NXP-Robotics/MR-NAVQ95/Design-files/Prototypes/Rev-B/96100_X-MR-NAVQ95E-CAM_B/BOM-96100_B.xlsx

X-MR-NAVQ95E-CAM Revised: Friday, January 16, 2026
SCH-96100 PDF: SPF-96100 Revision: B
Bill Of Materials January 16,2026 14:46:54 | Page1
Item | Quantity | AgilePN | ASSY_OPT | FIND# | PRE_APN | Reference | MFG_NAME01 | MFG_PN01 | Description
______________________________________________
1 | 4 | 280-10222 |  |  |  | BH1,BH2,BH3,BH4 |  |  | MOUNTING HOLE DRILL 3.7MM PAD 6MM PLATED TH NO PART TO ORDER
2 | 6 | 150-79025 |  |  |  | C6,C10,C11,C12,C13,C14 | MURATA | GCM155R71C104KA55D | CAP CER 0.1uF 16V 10% X7R AEC-Q200 0402
3 | 3 | 150-81359 |  |  |  | C7,C8,C9 | MURATA | GRM155Z71A105KE01J | CAP CER 1uF 10V 10% X7R 0402
4 | 4 | 480-79837 |  |  |  | D1,D2,D3,D4 | NEXPERIA | IP4292CZ10-TBR,115 | DIODE ESD TVS ARRAY USB2 USB3 5.5V 4A DFN2510A-10
5 | 1 | 480-78454 |  |  |  | D5 | NEXPERIA | PESD5V0F1BL,315 | DIODE BIDIR 1-LINE ESD PROT 0.4pF 6V 2.5A AEC-Q101 SOD882
6 | 2 | 150-81001 |  |  |  | FL1,FL2 | MURATA | NFM15PC104R1A3D | CAP FILTER EMI 0.1uF 10V 20% -- 0402
7 | 1 | 211-10508 |  |  |  | J1 | HIROSE | DF40TC-40DP-0.4V(51) | CON 2X20 PLUG SHRD SMT 0.4MM SP 51H AU
8 | 1 | 211-10530 |  |  |  | J3 | AMPHENOL | F32Q-1A7H1-11022 | CON 1X22 FPC/FFC RA SMT UPPER CONTACT 0.5MM SP 87H AU
9 | 1 | 210-80138 | DNP |  |  | J4 | SAMTEC | TSW-103-08-F-S-RA | HDR 1X3 RA TH 100MIL SP 124H AU 90L
10 | 1 | 470-82834 |  |  |  | R5 | VISHAY INTERTECHNOLOGY | CRCW0402200KFKEDC | RES MF 200K 1/16W 1% 0402
11 | 5 | 470-10144 |  |  |  | R8,R9,R10,R42,R43 | YAGEO AMERICA | AC0402JR-070RL | RES MF ZERO OHM JUMPER 1/16W 5% AEC-Q200 0402
12 | 4 | 470-82016 |  |  |  | R38,R39,R40,R41 | VISHAY INTERTECHNOLOGY | CRCW04022K20FKED | RES MF 2.2K 1/16W 1% AEC-Q200 0402
13 | 1 | 510-75618 |  |  |  | TP1 |  |  | TEST POINT PAD .035 SMT, no part to order
14 | 1 | 315-84354 |  |  |  | U1 | NXP SEMICONDUCTOR | PCA9306JKZ | IC DUAL BI I2C BUS SMBUS VOLTAGE TRANSLATOR 1-3.6V/1.8-5.5V X2SON8
