NXP-Robotics/MR-NAVQ95/Design-files/Prototypes/Rev-B/96101_X-MR-NAVQ95E-T1S_B/BOM-96101_B.xlsx

X-MR-NAVQ95E-T1S Revised: Friday, January 16, 2026
SCH-96101 PDF: SPF-96101 Revision: B
Bill Of Materials January 16,2026 14:53:41 | Page1
Item | Quantity | AgilePN | ASSY_OPT | FIND# | PRE_APN | Reference | MFG_NAME01 | MFG_PN01 | Description
______________________________________________
1 | 3 | 280-10222 |  |  |  | BH1,BH2,BH3 |  |  | MOUNTING HOLE DRILL 3.7MM PAD 6MM PLATED TH NO PART TO ORDER
2 | 1 | 150-79025 |  |  |  | C6 | MURATA | GCM155R71C104KA55D | CAP CER 0.1uF 16V 10% X7R AEC-Q200 0402
3 | 11 | 150-79497 |  |  |  | C126,C138,C139,C155,C165, | MURATA | GCM155C71A105KE38D | CAP CER 1uF 10V 10% X7S AEC-Q200 0402
 |  |  |  |  |  | C167,C173,C430,C432,C439,
 |  |  |  |  |  | C441
4 | 37 | 150-79461 |  |  |  | C127,C134,C137,C140,C146, | MURATA | GCM155R71H104KE02D | CAP CER 0.1uF 50V 10% X7R AEC-Q200 0402
 |  |  |  |  |  | C178,C423,C424,C431,C434,
 |  |  |  |  |  | C435,C444,C445,C446,C447,
 |  |  |  |  |  | C448,C449,C450,C451,C454,
 |  |  |  |  |  | C455,C457,C458,C459,C460,
 |  |  |  |  |  | C461,C462,C463,C464,C503,
 |  |  |  |  |  | C504,C506,C507,C508,C509,
 |  |  |  |  |  | C510,C511
5 | 2 | 150-80512 |  |  |  | C141,C505 | MURATA | GCJ21AR72E472KXJ1D | CAP CER 4700pF 250V 10% X7R AEC-Q200 0805
6 | 27 | 150-80277 |  |  |  | C149,C153,C220,C376,C378, | TDK | CGA2B3X7R1E104K050BB | CAP CER 0.1uF 25V 10% X7R AEC-Q200 0402
 |  |  |  |  |  | C389,C392,C402,C404,C425,
 |  |  |  |  |  | C426,C467,C469,C471,C477,
 |  |  |  |  |  | C479,C488,C489,C490,C491,
 |  |  |  |  |  | C492,C514,C524,C526,C527,
 |  |  |  |  |  | C528,C529
7 | 11 | 150-75772 |  |  |  | C150,C154,C169,C470,C483, | YAGEO AMERICA | CC0402KRX5R6BB105 | CAP CER 1.0UF 10V 10% X5R 0402
 |  |  |  |  |  | C484,C485,C486,C487,C515,
 |  |  |  |  |  | C530
8 | 2 | 150-80967 |  |  |  | C151,C152 | MURATA | GRT188R61C106KE13D | CAP CER 10uF 16V 10% X5R AEC-Q200 0603
9 | 2 | 150-79365 | DNP |  |  | C156,C456 | MURATA | GCM155R71E103KA37D | CAP CER 0.01uF 25V 10% X7R AEC-Q200 0402
10 | 53 | 150-80124 |  |  |  | C159,C170,C171,C172,C174, | MURATA | GRM033Z71C104KE14 | CAP CER 0.1uF 16V 10% X7R 0201
 |  |  |  |  |  | C175,C176,C177,C179,C180,
 |  |  |  |  |  | C181,C182,C183,C184,C186,
 |  |  |  |  |  | C187,C188,C191,C192,C193,
 |  |  |  |  |  | C194,C195,C196,C201,C203,
 |  |  |  |  |  | C205,C206,C207,C211,C212,
 |  |  |  |  |  | C213,C217,C218,C219,C221,
 |  |  |  |  |  | C222,C223,C226,C230,C231,
 |  |  |  |  |  | C232,C233,C234,C235,C236,
 |  |  |  |  |  | C237,C238,C472,C474,C497,
 |  |  |  |  |  | C498,C499,C500
11 | 1 | 150-79272 |  |  |  | C202 | MURATA | GRM188R61E106MA73D | CAP CER 10uF 25V 20% X5R 0603
12 | 1 | 150-78979 |  |  |  | C204 | TDK | C2012X5R1A476M125AC | CAP CER 47uF 10V 20% X5R 0805
13 | 6 | 150-80055 |  |  |  | C375,C388,C401,C422,C466, | YAGEO AMERICA | AC0603KRX7R0BB472 | CAP CER 4700pF 100V 10% X7R AEC-Q200 0603
 |  |  |  |  |  | C475
14 | 6 | 150-81481 |  |  |  | C398,C399,C403,C407,C408, | MURATA | GRT21BD71A226ME13 | CAP CER 22uF 10V 20% X7T AEC-Q200 0805
 |  |  |  |  |  | C411
15 | 2 | 150-76336 |  |  |  | C452,C468 | MURATA | GJM1555C1H8R0CB01D | CAP CER 8.0pF 50V 3.12% C0G 0402
16 | 6 | 150-80340 |  |  |  | C481,C482,C501,C502,C512, | MURATA | GCM033C70J104KE02D | CAP CER 0.1uF 6.3V 10% X7S AEC-Q200 0201
 |  |  |  |  |  | C513
17 | 3 | 150-81482 |  |  |  | C493,C495,C496 | MURATA | GRT188C71C475KE13 | CAP CER 4.7uF 16V 10% X7S AEC-Q200 0603
18 | 1 | 150-79362 |  |  |  | C494 | MURATA | GCM32ER71C226KE19L | CAP CER 22uF 16V 10% X7R AEC-Q200 1210
19 | 2 | 150-81792 |  |  |  | C516,C517 | MURATA | GCM31C5C3A102JX03 | CAP CER 1000pF 1000V 5% C0G AEC-Q200 1206
20 | 2 | 150-81359 |  |  |  | C521,C525 | MURATA | GRM155Z71A105KE01J | CAP CER 1uF 10V 10% X7R 0402
21 | 2 | 370-76859 |  |  |  | D33,D35 | WURTH ELEKTRONIK EISOS GMBH & CO. KG (ELECTRONIC & ELECTROMEHANICAL COMP) | 150060AS75000 | LED AMB SGL 2V 20mA 0603
22 | 2 | 370-76670 |  |  |  | D34,D36 | WURTH ELEKTRONIK EISOS GMBH & CO. KG (ELECTRONIC & ELECTROMEHANICAL COMP) | 150060VS75000 | LED BRIGHT GRN SGL 30mA 0603
23 | 8 | 480-80185 |  |  |  | U57,U64,D66,D68,D70,D72, | NEXPERIA | PESD2ETH1G-T | DIODE 2 CH ESD PROTECTOR 30KV 24V AEC-Q101 SOT23
 |  |  |  |  |  | D74,D76
24 | 6 | 370-76565 |  |  |  | D67,D69,D71,D73,D75,D77 | OSRAM | LG L29K-G2J1-24-Z | LED GRN SGL 20MA 0603
25 | 1 | 370-76464 |  |  |  | D79 | KINGBRIGHT | APT1608MGC | LED GRN SGL 30MA SMT
26 | 6 | 211-80595 |  |  |  | J26,J27,J28,J29,J30,J31 | JST MFG. CO | SM02B-GHS-TB(LF)(SN) | CON 1X2 CRIMP RA 1.25MM SP 173H SN SMT
27 | 2 | 210-83192 |  |  |  | J32,J35 | HARTING | 9452812800 | CON 1X2 JACK 1 PORT TH 2.8MM SP 244H -- 91L
28 | 1 | 211-10510 |  |  |  | J33 | HIROSE | DF40TC-50DP-0.4V(51) | CON 2X25 PLUG SHRD SMT 0.4MM SP 51H AU
29 | 1 | 210-80888 |  |  |  | J37 | SAMTEC | SHF-105-01-L-D-RA | CON 2X5 TH SHRD PLUG RA 50MIL CTR 225H AU 75L
30 | 3 | 180-78924 |  |  |  | LBK1,LBK2,LBK3 | TDK | TFM252012ALMAR47MTAA | IND PWR 0.47uH@1MHz 5.8A 20% AEC-Q200 SMT
31 | 10 | 180-81335 |  |  |  | L13,L14,L15,L18,L19,L21, | Murata Electronics | BLM15AG121SH1D | IND FER BEAD 120 OHM@100MHZ 0.5A 0.25 OHM 25% AEC-Q200 0402
 |  |  |  |  |  | L41,L42,L44,L46
32 | 11 | 180-78156 |  |  |  | L16,L17,L23,L48,L50,L51, | TDK | MPZ1608S331A | IND FER BEAD 330OHM@100MHZ 1.7A 0603
 |  |  |  |  |  | L52,L53,L54,L56,L57
33 | 6 | 180-78762 |  |  |  | L35,L37,L39,L40,L47,L49 | TDK | ACT1210L-201-2P-TL00 | FILTER COMMON MODE 200uH@100KHZ 70mA +30/-10% AEC-Q200 SMT
34 | 2 | 180-81135 |  |  |  | L45,L55 | MURATA | DLW32MH101XT2 | IND CHK COMMON MODE 100uH@100KHz 100mA 2.6 OHM -25-50% AEC-Q200 SMT
35 | 1 | 470-82834 |  |  |  | R5 | VISHAY INTERTECHNOLOGY | CRCW0402200KFKEDC | RES MF 200K 1/16W 1% 0402
36 | 6 | 470-82056 |  |  |  | R93,R160,R565,R605,R606, | VISHAY INTERTECHNOLOGY | CRCW0402100KJNED | RES MF 100K 1/16W 5% AEC-Q200 0402
 |  |  |  |  |  | R607
37 | 4 | 470-80911 |  |  |  | R170,R173,R229,R230 | YAGEO | RC0402FR-074K7L | RES MF 4.7K OHM 1/16W 1% 0402
38 | 1 | 470-83291 |  |  |  | R171 | YAGEO AMERICA | RC0402FR-071K2L | RES MF 1.2K 1% 1/16W 0402
39 | 2 | 470-81931 |  |  |  | R184,R561 | ROHM | ESR10EZPF1003 | RES MF 100K 0.4W 1% AEC-Q200 0805
40 | 16 | 470-81930 |  |  |  | R186,R187,R454,R462,R465, | ROHM | ESR10EZPF1001 | RES MF 1.0K 0.4W 1% AEC-Q200 0805
 |  |  |  |  |  | R470,R481,R490,R501,R517,
 |  |  |  |  |  | R532,R536,R538,R540,R559,
 |  |  |  |  |  | R560
41 | 28 | 470-80881 |  |  |  | R191,R193,R194,R195,R200, | VISHAY INTERTECHNOLOGY | CRCW040210K0FKEDHP | RES MF 10K 1/5W 1% AEC-Q200 0402
 |  |  |  |  |  | R209,R213,R215,R216,R218,
 |  |  |  |  |  | R220,R222,R223,R224,R225,
 |  |  |  |  |  | R226,R227,R228,R504,R505,
 |  |  |  |  |  | R508,R509,R512,R518,R519,
 |  |  |  |  |  | R531,R550,R601
42 | 1 | 470-81665 |  |  |  | R208 | KOA SPEER | RK73H1ETTP6491F | RES MF 6.49K 1/10W 1% AEC-Q200 0402
43 | 19 | 470-82894 |  |  |  | R211,R551,R562,R563,R571, | VISHAY | RCC04020000Z0ED | RES MF ZERO OHM 1/8W -- AEC-Q200 0402
 |  |  |  |  |  | R572,R577,R578,R579,R580,
 |  |  |  |  |  | R587,R588,R589,R604,R609,
 |  |  |  |  |  | R610,R611,R612,R613
44 | 4 | 470-77301 |  |  |  | R231,R232,R233,R234 | PANASONIC | ERJ-2GEJ681X | RES MF 680 OHM 1/16W 5% 0402
45 | 6 | 470-81181 |  |  |  | R459,R466,R489,R515,R535, | VISHAY INTERTECHNOLOGY | CRCW0603100KFKEAHP | RES MF 100K 1/4W 1% AEC-Q200 0603
 |  |  |  |  |  | R539
46 | 6 | 470-30776 |  |  |  | R464,R473,R493,R520,R537, | WALSIN TECHNOLOGY CORP. | WR04X2400FTL | RES MF 240 OHM 1/16W 1% 0402
 |  |  |  |  |  | R541
47 | 6 | 470-80881 | DNP |  |  | R506,R507,R511,R547,R548, | VISHAY INTERTECHNOLOGY | CRCW040210K0FKEDHP | RES MF 10K 1/5W 1% AEC-Q200 0402
 |  |  |  |  |  | R555
48 | 8 | 470-82894 | DNP |  |  | R552,R567,R568,R569,R584, | VISHAY | RCC04020000Z0ED | RES MF ZERO OHM 1/8W -- AEC-Q200 0402
 |  |  |  |  |  | R585,R586,R597
49 | 1 | 470-83520 |  |  |  | R558 | YAGEO | AC0402JR-07100RL | RES MF 100 OHM 1/16W 5% AEC-Q200 0402
50 | 2 | 470-81628 |  |  |  | R564,R566 | KOA SPEER | RK73H1ETTP5101F | RES MF 5.1K 1/10W 1% AEC-Q200 0402
51 | 4 | 470-81990 |  |  |  | R573,R593,R594,R596 | KOA SPEER | RK73H1ETTP1501F | RES MF 1.50K 1/10W 1% AEC-Q200 0402
52 | 2 | 470-81990 | DNP |  |  | R574,R595 | KOA SPEER | RK73H1ETTP1501F | RES MF 1.50K 1/10W 1% AEC-Q200 0402
53 | 2 | 470-10187 |  |  |  | R590,R591 | YAGEO AMERICA | VT1206FRE071ML | RES MF 1M 1/4W 1% AEC-Q200 1206
54 | 2 | 470-82544 |  |  |  | R602,R603 | YAGEO AMERICA | AC0402FR-072K2L | RES MF 2.2K 1/16W 1% AEC-Q200 0402
55 | 1 | 470-82056 | DNP |  |  | R608 | VISHAY INTERTECHNOLOGY | CRCW0402100KJNED | RES MF 100K 1/16W 5% AEC-Q200 0402
56 | 1 | 510-78644 |  |  |  | S1 | NIDEC COPAL ELECTRONICS CORP | CHS-02TA | SW SPST SLD WSH 25MA 24V DIP-2 SMT
57 | 8 | 510-75618 |  |  |  | TP21,TP22,TP245,TP248, |  |  | TEST POINT PAD .035 SMT, no part to order
 |  |  |  |  |  | TP249,TP250,TP251,TP252
58 | 1 | 312-82081 |  |  |  | U53 | ISSI | IS25LP080D-JNLE-TR | IC SERIAL FLASH MEMORY SPI 128BIT 2.30V 3.60V SOIC8 DATE CODE MUST BE 1925 OR HIGHER
59 | 2 | 312-83772 |  |  |  | U54,U55 | NXP SEMICONDUCTORS | TJA1120BHN | IC ETH PHY 3.3V AEC-Q100 HVQFN36
60 | 1 | 330-77155 |  |  |  | U58 | NXP SEMICONDUCTOR | SJA1110AEL | IC ETHERNET SW WITH EMBEDDED PHYS AND CPU 3.3V AUTO BGA256A
61 | 1 | 315-10678 |  |  |  | U63 | NXP SEMICONDUCTOR | PPF5103AMMAFES | IC POWER MANAGEMENT 5.5V AEC-Q100 QFN28
62 | 1 | 315-84354 |  |  |  | U65 | NXP SEMICONDUCTOR | PCA9306JKZ | IC DUAL BI I2C BUS SMBUS VOLTAGE TRANSLATOR 1-3.6V/1.8-5.5V X2SON8
63 | 1 | 230-78230 |  |  |  | X1 | MURATA | XRCGB25M000F3A00R0 | XTAL 25.000MHZ 30PPM 6PF AEC-Q200 SMT
