NXP-Robotics/MR-NAVQ95/MR-NAVQ95-cheatsheet.pdf

MR-NAVQ95 PINOUT CHEAT SHEET | IO expansion board (NAVQ95-IO) | SHEET 1 / 2

## J9 PWM

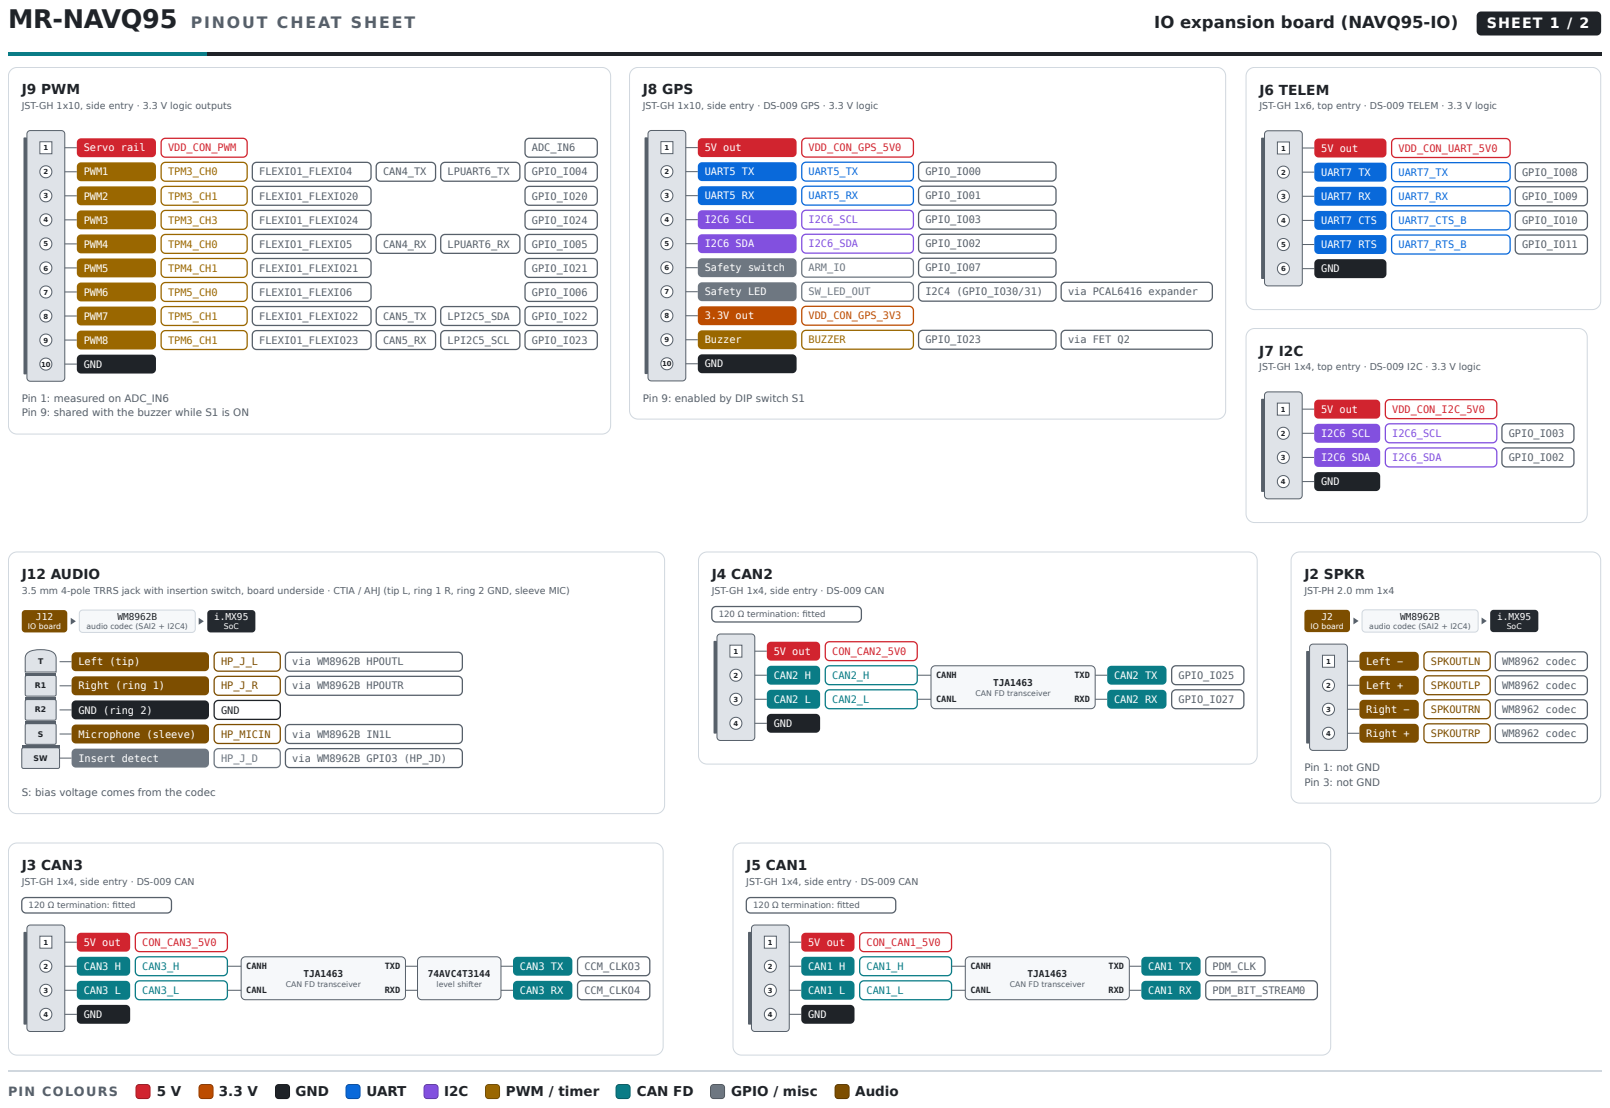
[picture p48: page 1]

J8 GPS
JST-GH 1x10, side entry · DS-009 GPS · 3.3 V logic

J6 TELEM
JST-GH 1x6, top entry · DS-009 TELEM · 3.3 V logic

JST-GH 1x10, side entry · 3.3 V logic outputs

JST-GH 1x4, top entry · DS-009 I2C · 3.3 V logic

Pin 1: measured on ADC_IN6
Pin 9: shared with the buzzer while S1 is ON

Pin 9: enabled by DIP switch S1

J12 AUDIO
3.5 mm 4-pole TRRS jack with insertion switch, board underside · CTIA / AHJ (tip L, ring 1 R, ring 2 GND, sleeve MIC)

J4 CAN2
JST-GH 1x4, side entry · DS-009 CAN

S: bias voltage comes from the codec

J3 CAN3

J5 CAN1

MR-NAVQ95 PINOUT CHEAT SHEET | Main board (NAVQ95-MAIN) and Camera expansion board (NAVQ95-CAMRP) | SHEET 2 / 2

## J16 M.2 KEY B

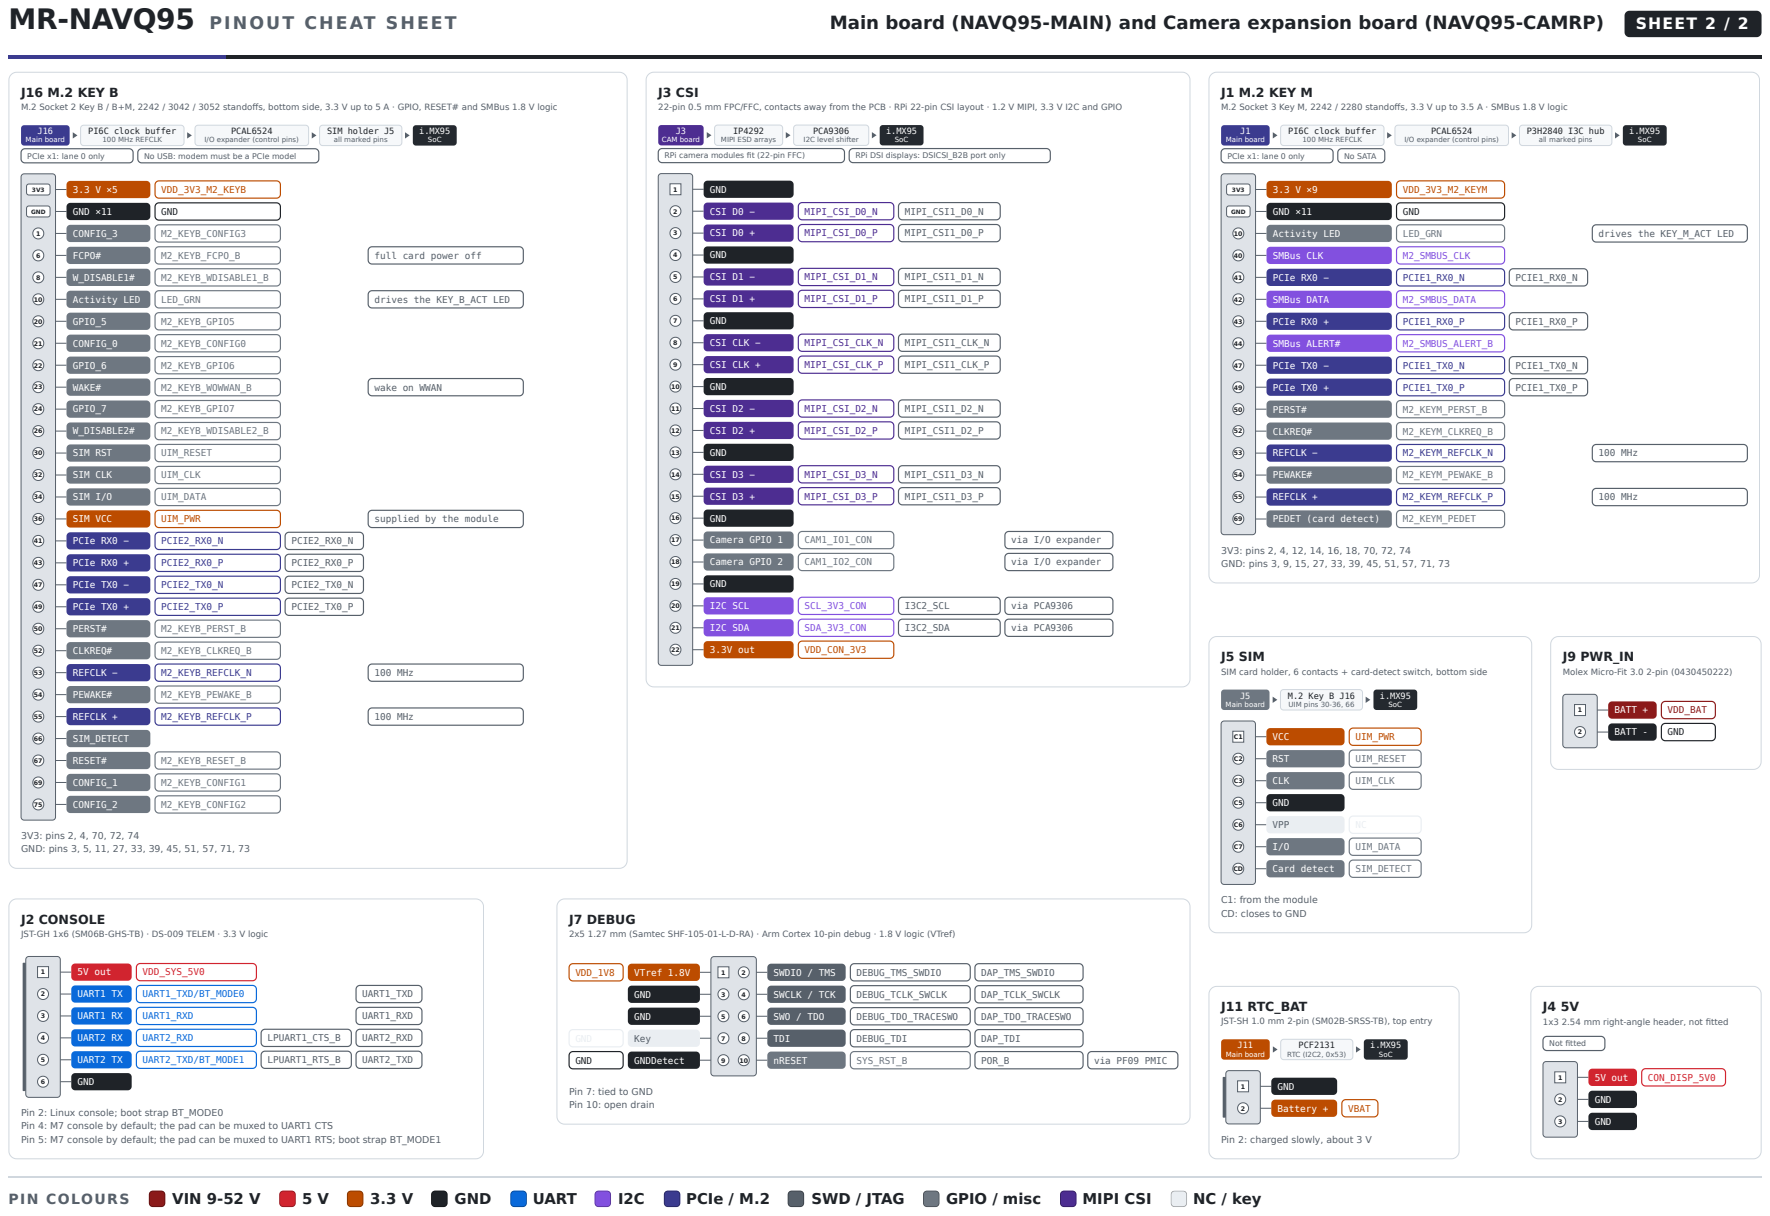
[picture p49: page 2]

M.2 Socket 2 Key B / B+M, 2242 / 3042 / 3052 standoffs, bottom side, 3.3 V up to 5 A · GPIO, RESET# and SMBus 1.8 V logic

J3 CSI
22-pin 0.5 mm FPC/FFC, contacts away from the PCB · RPi 22-pin CSI layout · 1.2 V MIPI, 3.3 V I2C and GPIO

J1 M.2 KEY M
M.2 Socket 3 Key M, 2242 / 2280 standoffs, 3.3 V up to 3.5 A · SMBus 1.8 V logic

J5 SIM
SIM card holder, 6 contacts + card-detect switch, bottom side

J9 PWR_IN
Molex Micro-Fit 3.0 2-pin (0430450222)

C1: from the module
CD: closes to GND

J2 CONSOLE
JST-GH 1x6 (SM06B-GHS-TB) · DS-009 TELEM · 3.3 V logic

J7 DEBUG
2x5 1.27 mm (Samtec SHF-105-01-L-D-RA) · Arm Cortex 10-pin debug · 1.8 V logic (VTref)

J11 RTC_BAT
JST-SH 1.0 mm 2-pin (SM02B-SRSS-TB), top entry

1x3 2.54 mm right-angle header, not fitted

Pin 7: tied to GND
Pin 10: open drain

Pin 2: Linux console; boot strap BT_MODE0
Pin 4: M7 console by default; the pad can be muxed to UART1 CTS
Pin 5: M7 console by default; the pad can be muxed to UART1 RTS; boot strap BT_MODE1

Pin 2: charged slowly, about 3 V
