NXP-Robotics/MR-NAVQ95/Schematic/Prototypes/Schematic-Rev-A/SPF-96098_A-T1PHY.pdf

5

4

3

2

1

D | D
C | C
B | B
A | A

# X-MR-NAVQ95E-T1P

DateRev.

# 1. Interrupted lines coded with the same letter or

letter combinations are electrically connected.

X0-X8

_B denotes an active-low signal.

# 6. All SILK display properties will be in this color

# YT (CTO SI)

By

# NOTES:

# Revision History

# 5. Interpret diagram in accordance with American National Standards Institute specifications, current

revision, with the exception of logic block symbology.

2. Device type number is for reference only. The number varies with the manufacturer.

# 7. All schematic annotations will be in this color

2025-09-12

# Description

_P and _N denote a differential signal.

# Initial schematic development and format changes

# 3. Greyed out components indicate

Do Not Populate (DNP) during assembly.

# 4. Special signal usage:

# Table of Contents

# P01 Cover P02 Notes P03 ETH_B2B P04 TJA1103BHN

# Schematic is released2025-09-16 YT (CTO SI)A

# P05 Changelog

# A detailed changelog is available on the last page

Drawing Title:

Size | Document Number | Rev
Date: | Sheet | of

Page Title:

Designer:

Drawn by:

Approved:

## System Innovation

High Tech Campus 60
5656 AG Eindhoven, The Netherlands This document contains information proprietary to NXP and shall not be used for engineering design, procurement or manufacture in whole or in part without the express written permission of NXP Semiconductors.
© | Classification:NXP SEMICONDUCTORS
SCH-96098 PDF: SPF-96098 | A

# X-MR-NAVQ95E-T1P

C

Monday, September 29, 2025

## Cover

Youri Tils

Jari van Ewijk

Youri Tils

1 | 5

Company Internal/Proprietary Drawing Title:

Size | Document Number | Rev
Date: | Sheet | of

Page Title:

Designer:

Drawn by:

Approved:

## System Innovation

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

# X-MR-NAVQ95E-T1P

C

Monday, September 29, 2025

## Cover

Youri Tils

Jari van Ewijk

Youri Tils

1 | 5

Company Internal/Proprietary Drawing Title:

Size | Document Number | Rev
Date: | Sheet | of

Page Title:

Designer:

Drawn by:

Approved:

## System Innovation

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

# X-MR-NAVQ95E-T1P

C

Monday, September 29, 2025

## Cover

Youri Tils

Jari van Ewijk

Youri Tils

1 | 5

Company Internal/Proprietary

REF DES | ASSY_OPT | PAGE NAME
R235,R239,R240,R562,R563 | DNP | P04-TJA1103BHN

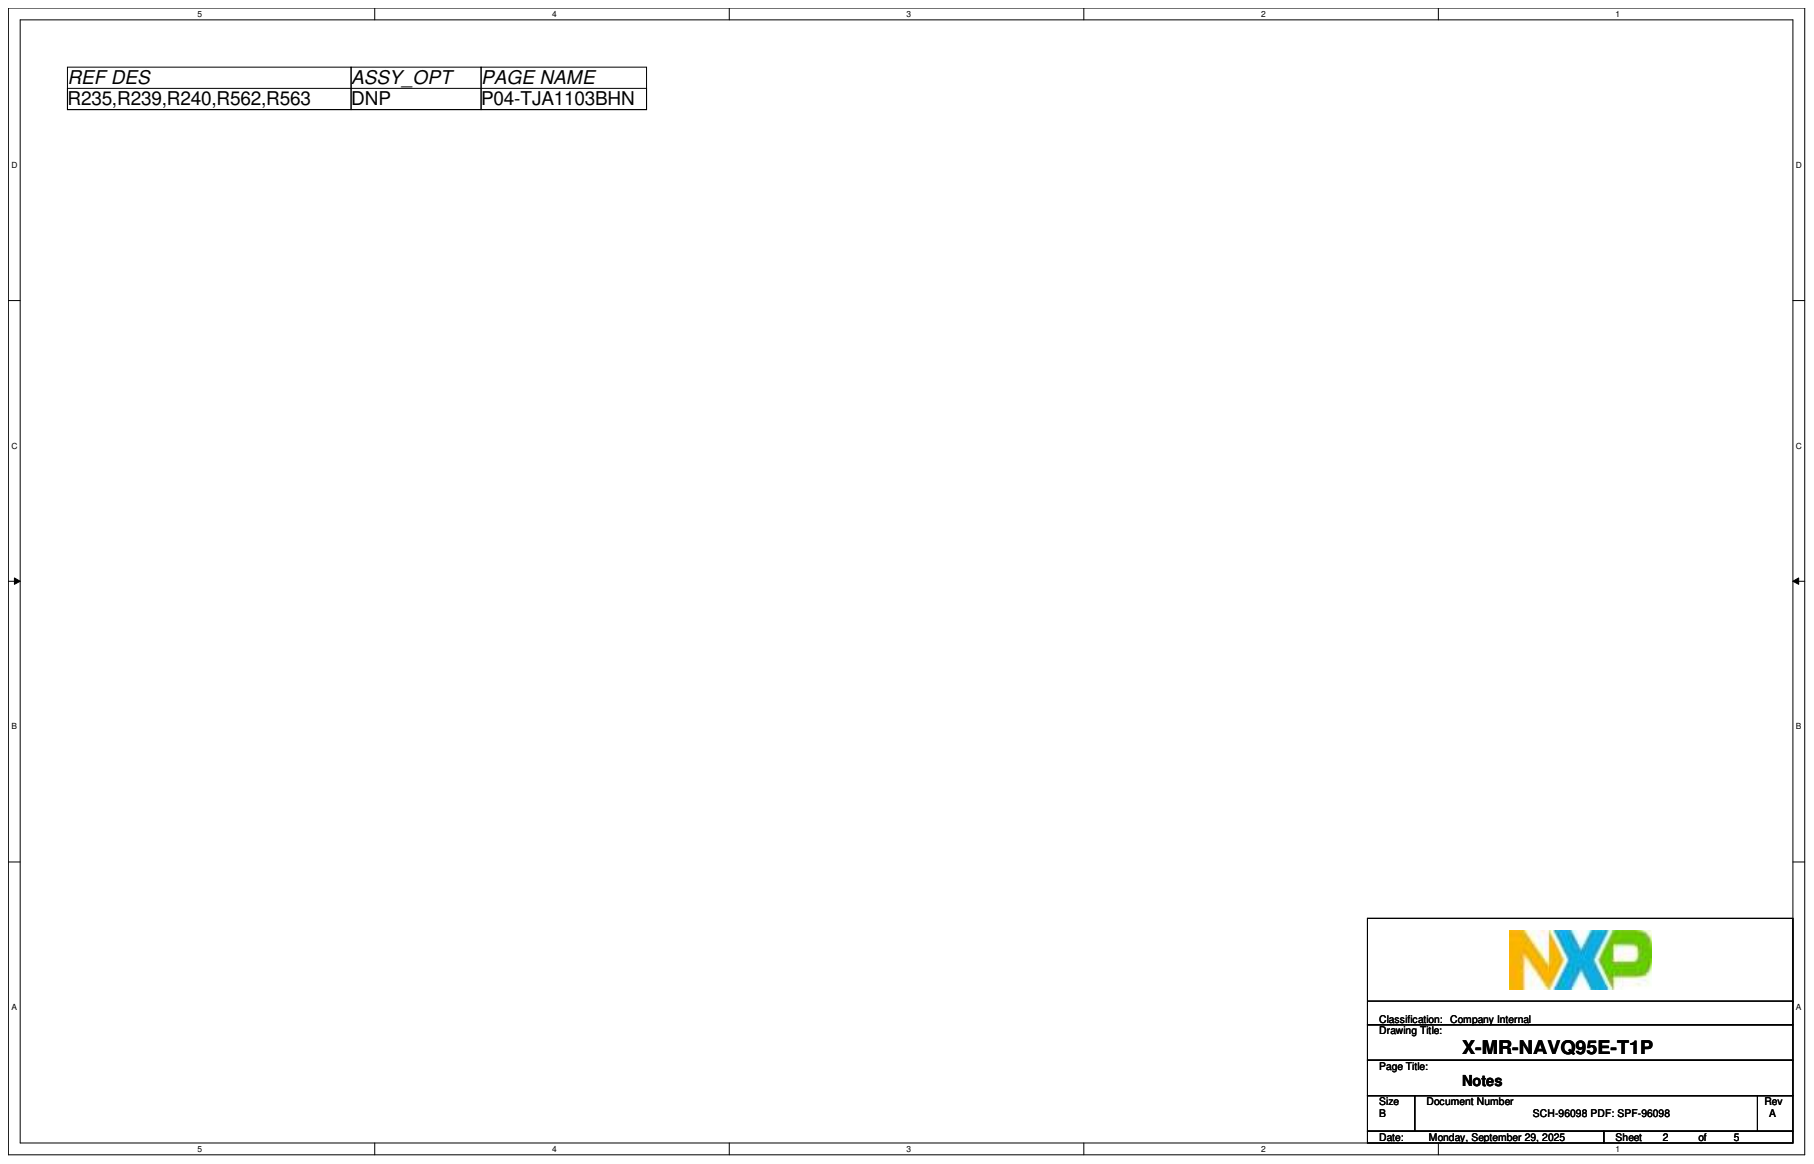
[picture p50: page 2]
Drawing Title:; Size; Document Number; Rev; Date:; Sheet; Page Title:; Classification:; SCH-96098 PDF: SPF-96098; X-MR-NAVQ95E-T1P; Monday, September 29, 2025; Notes; Company Internal

## Layout Note: Differential Pair

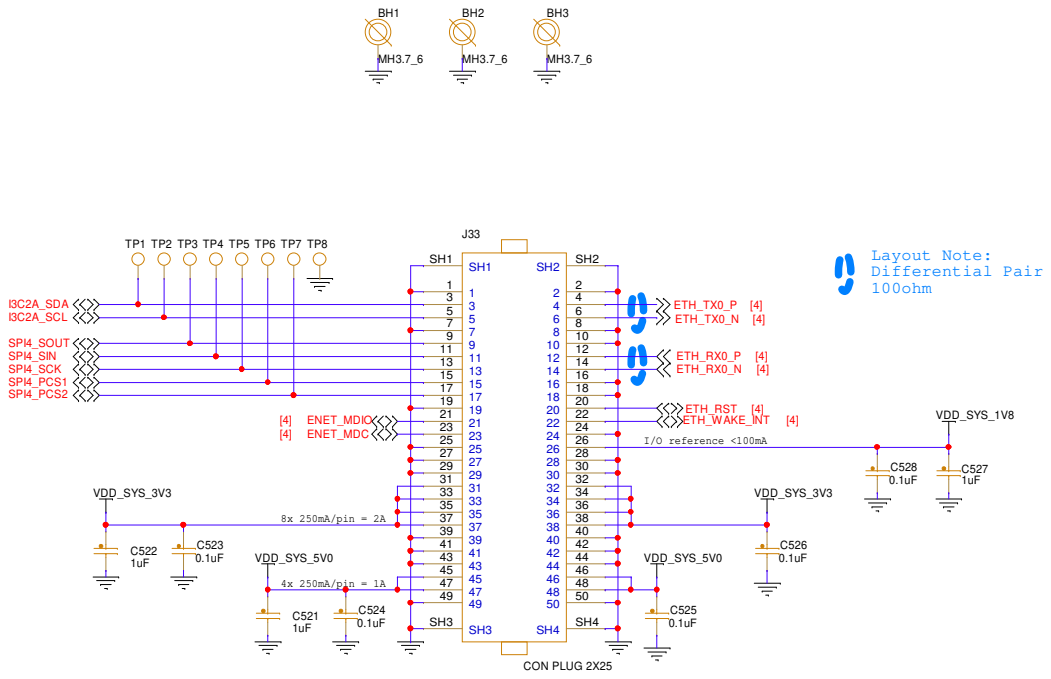
[picture p51: page 3]

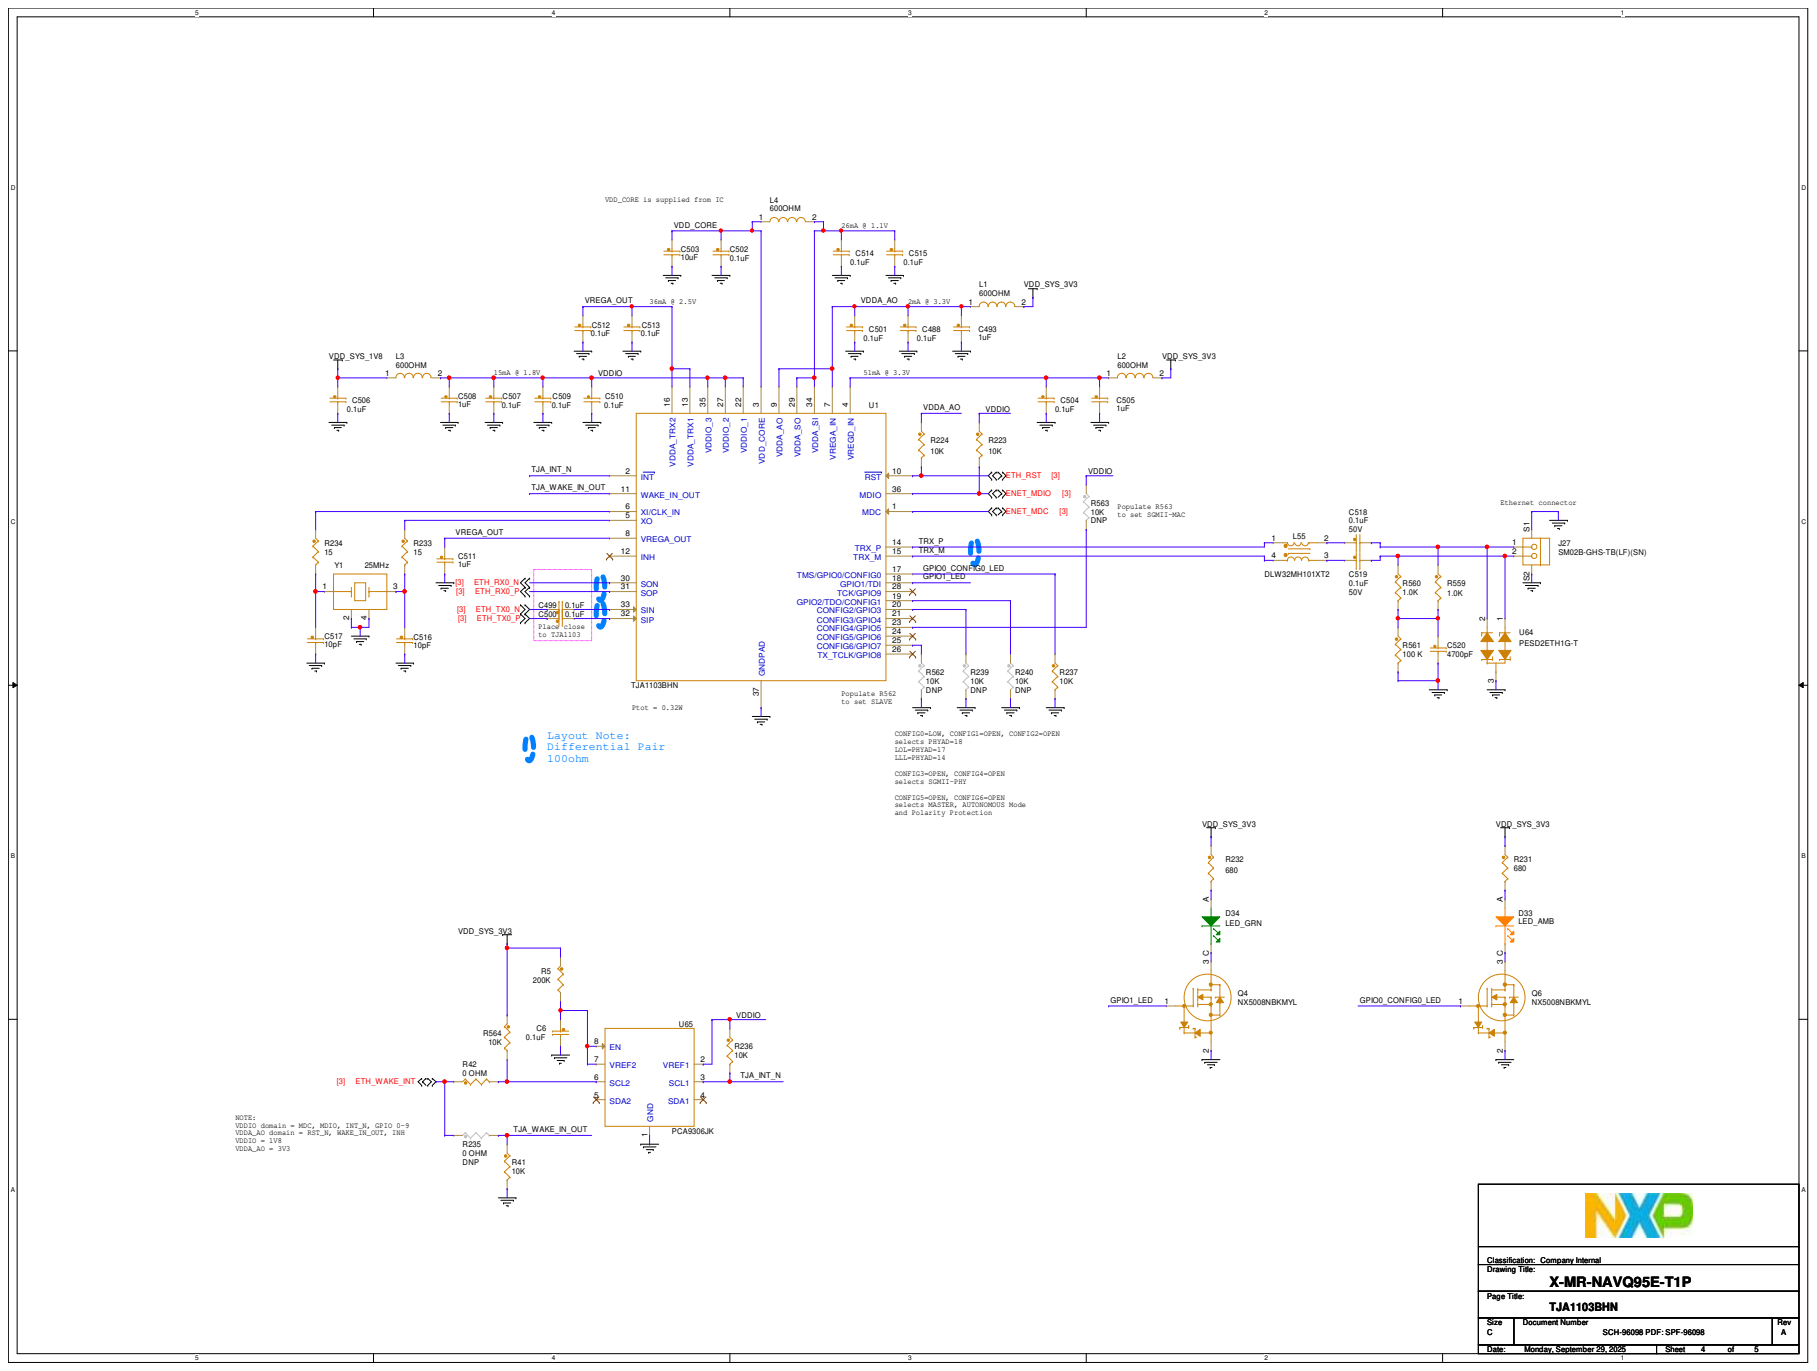
[picture p52: page 4]

VDD_CORE is supplied from IC

Populate R563
to set SGMII-MAC

CONFIG5=OPEN, CONFIG6=OPEN
selects MASTER, AUTONOMOUS Mode
and Polarity Protection

5-09-12 | YT (CTO SI)X0-X5 | Initial schematic development and format changes202

# Added note for VDD_CORE and MOSFET circuit

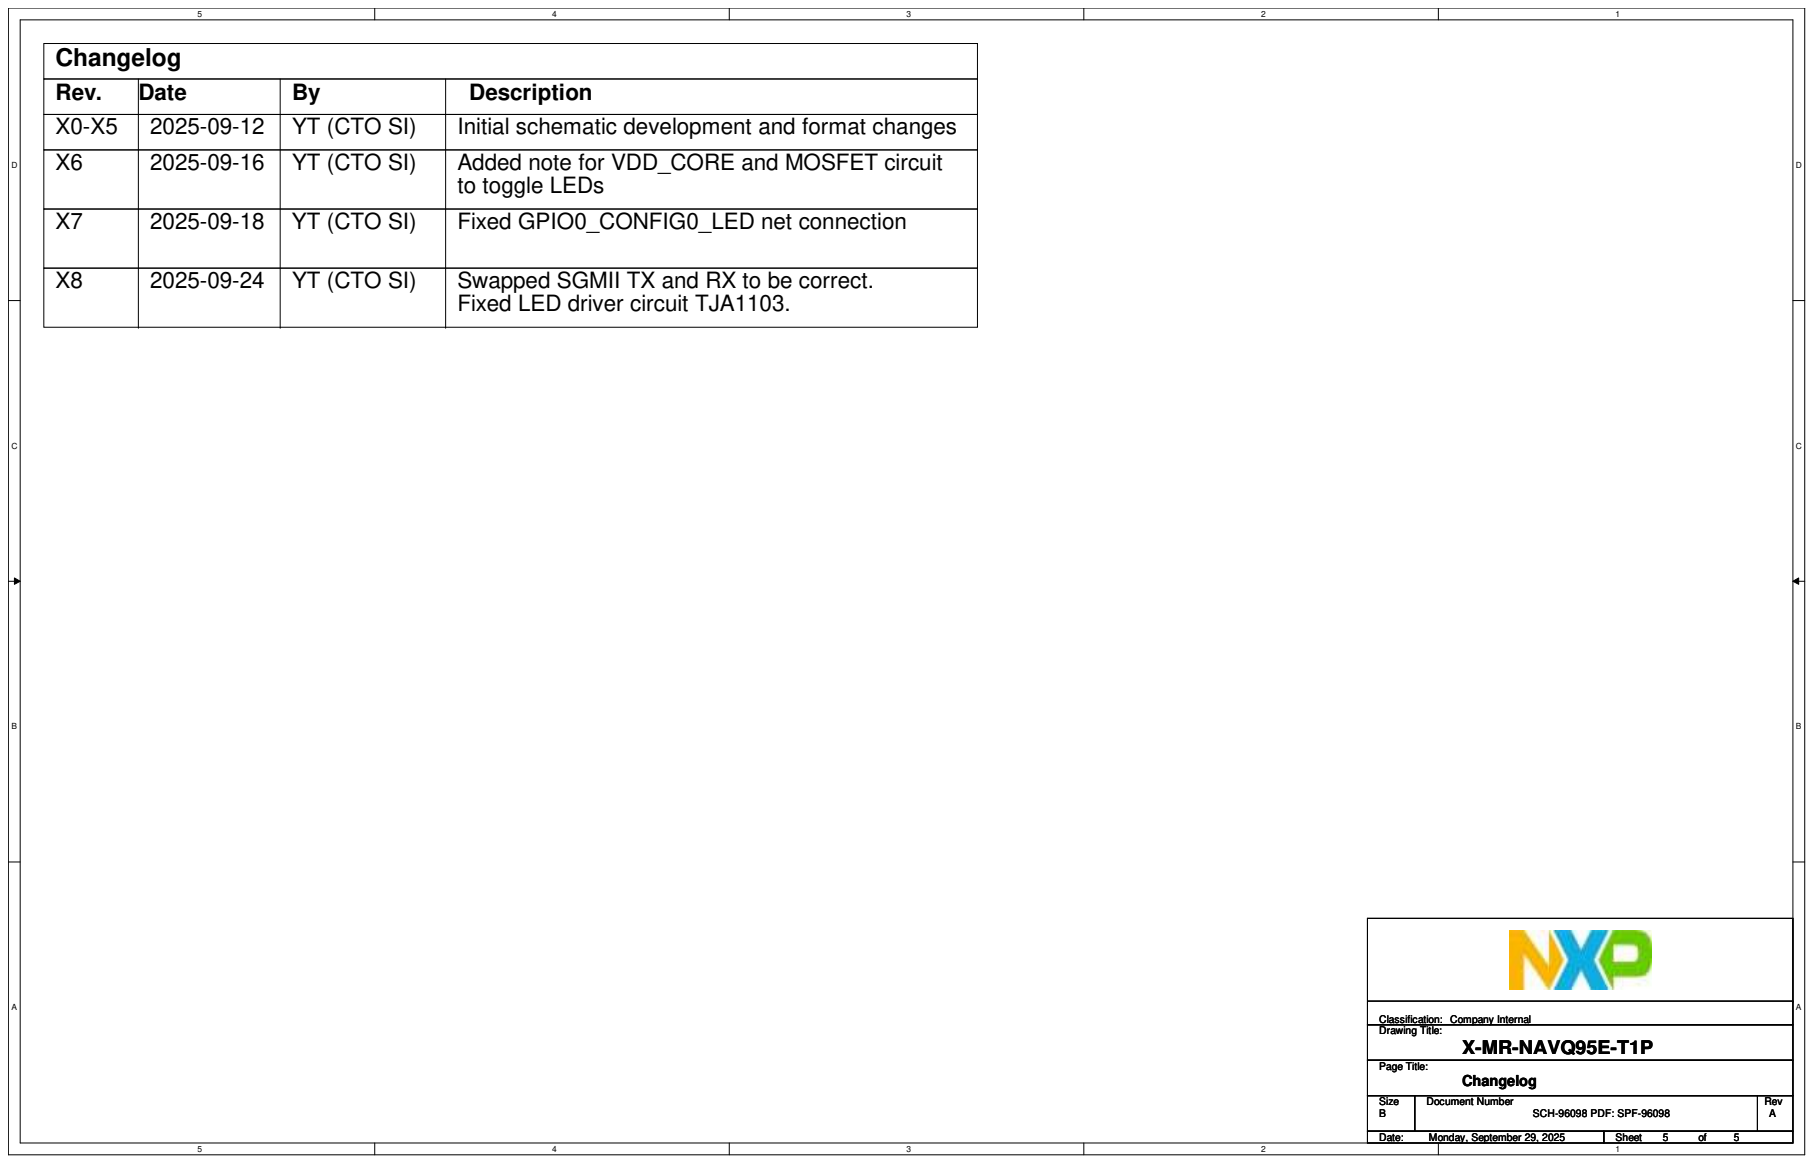
[picture p53: page 5]
Fixed GPIO0_CONFIG0_LED net connection2025-09-18; YT (CTO SI); YT (CTO SI)X8; Rev.; Changelog; DescriptionDate; Drawing Title:; Size; Document Number; Rev; Date:; Sheet; Page Title:; Classification:; SCH-96098 PDF: SPF-96098; X-MR-NAVQ95E-T1P; Monday, September 29, 2025; Company Internal

YT (CTO SI)2025-09-16X6

to toggle LEDs

Swapped SGMII TX and RX to be correct.
Fixed LED driver circuit TJA1103.
