NXP-Robotics/MR-NAVQ95/Schematic/Prototypes/Schematic-Rev-A/SPF-96099_A-IO.pdf

5

4

3

2

1

D | D
C | C
B | B
A | A

# 1. Interrupted lines coded with the same letter or

letter combinations are electrically connected.

5-09-11 | Initial schematic development and format changes202

# X-MR-NAVQ95E-IO

# 5. Interpret diagram in accordance with American National Standards Institute specifications, current

revision, with the exception of logic block symbology.

By

_B denotes an active-low signal.

Rev.

# 4. Special signal usage:

_P and _N denote a differential signal.

# 7. All schematic annotations will be in this color

# Revision History

# YT (CTO SI)X0-X9

# Date

# 3. Greyed out components indicate

Do Not Populate (DNP) during assembly.

# Description

2. Device type number is for reference only. The number varies with the manufacturer.

# NOTES:

# 6. All SILK display properties will be in this color

# Table of Contents

# P01 Cover P02 Notes P03 B2B P04 CAN P05 Sensors_and_IO P06 Console

A | 2025-09-26 | YT (CTO SI) | Schematic is released

# ChangelogP07

Drawing Title:

Size | Document Number | Rev
Date: | Sheet | of

Page Title:

Designer:

Drawn by:

Approved:

## System Innovation

High Tech Campus 60
5656 AG Eindhoven, The Netherlands This document contains information proprietary to NXP and shall not be used for engineering design, procurement or manufacture in whole or in part without the express written permission of NXP Semiconductors.
© | Classification:NXP SEMICONDUCTORS
SCH-96099 PDF: SPF-96099 | A

# X-MR-NAVQ95E-IO

C

Monday, September 29, 2025

## Cover

Youri Tils

Jari van Ewijk

Youri Tils

1 | 7

Company Internal/Proprietary Drawing Title:

Size | Document Number | Rev
Date: | Sheet | of

Page Title:

Designer:

Drawn by:

Approved:

## System Innovation

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

# X-MR-NAVQ95E-IO

C

Monday, September 29, 2025

## Cover

Youri Tils

Jari van Ewijk

Youri Tils

1 | 7

Company Internal/Proprietary Drawing Title:

Size | Document Number | Rev
Date: | Sheet | of

Page Title:

Designer:

Drawn by:

Approved:

## System Innovation

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

# X-MR-NAVQ95E-IO

C

Monday, September 29, 2025

## Cover

Youri Tils

Jari van Ewijk

Youri Tils

1 | 7

Company Internal/Proprietary

REF DES | ASSY_OPT | PAGE NAME
R5,R8,R12,R36,R38,R39 | DNP | P04-CAN

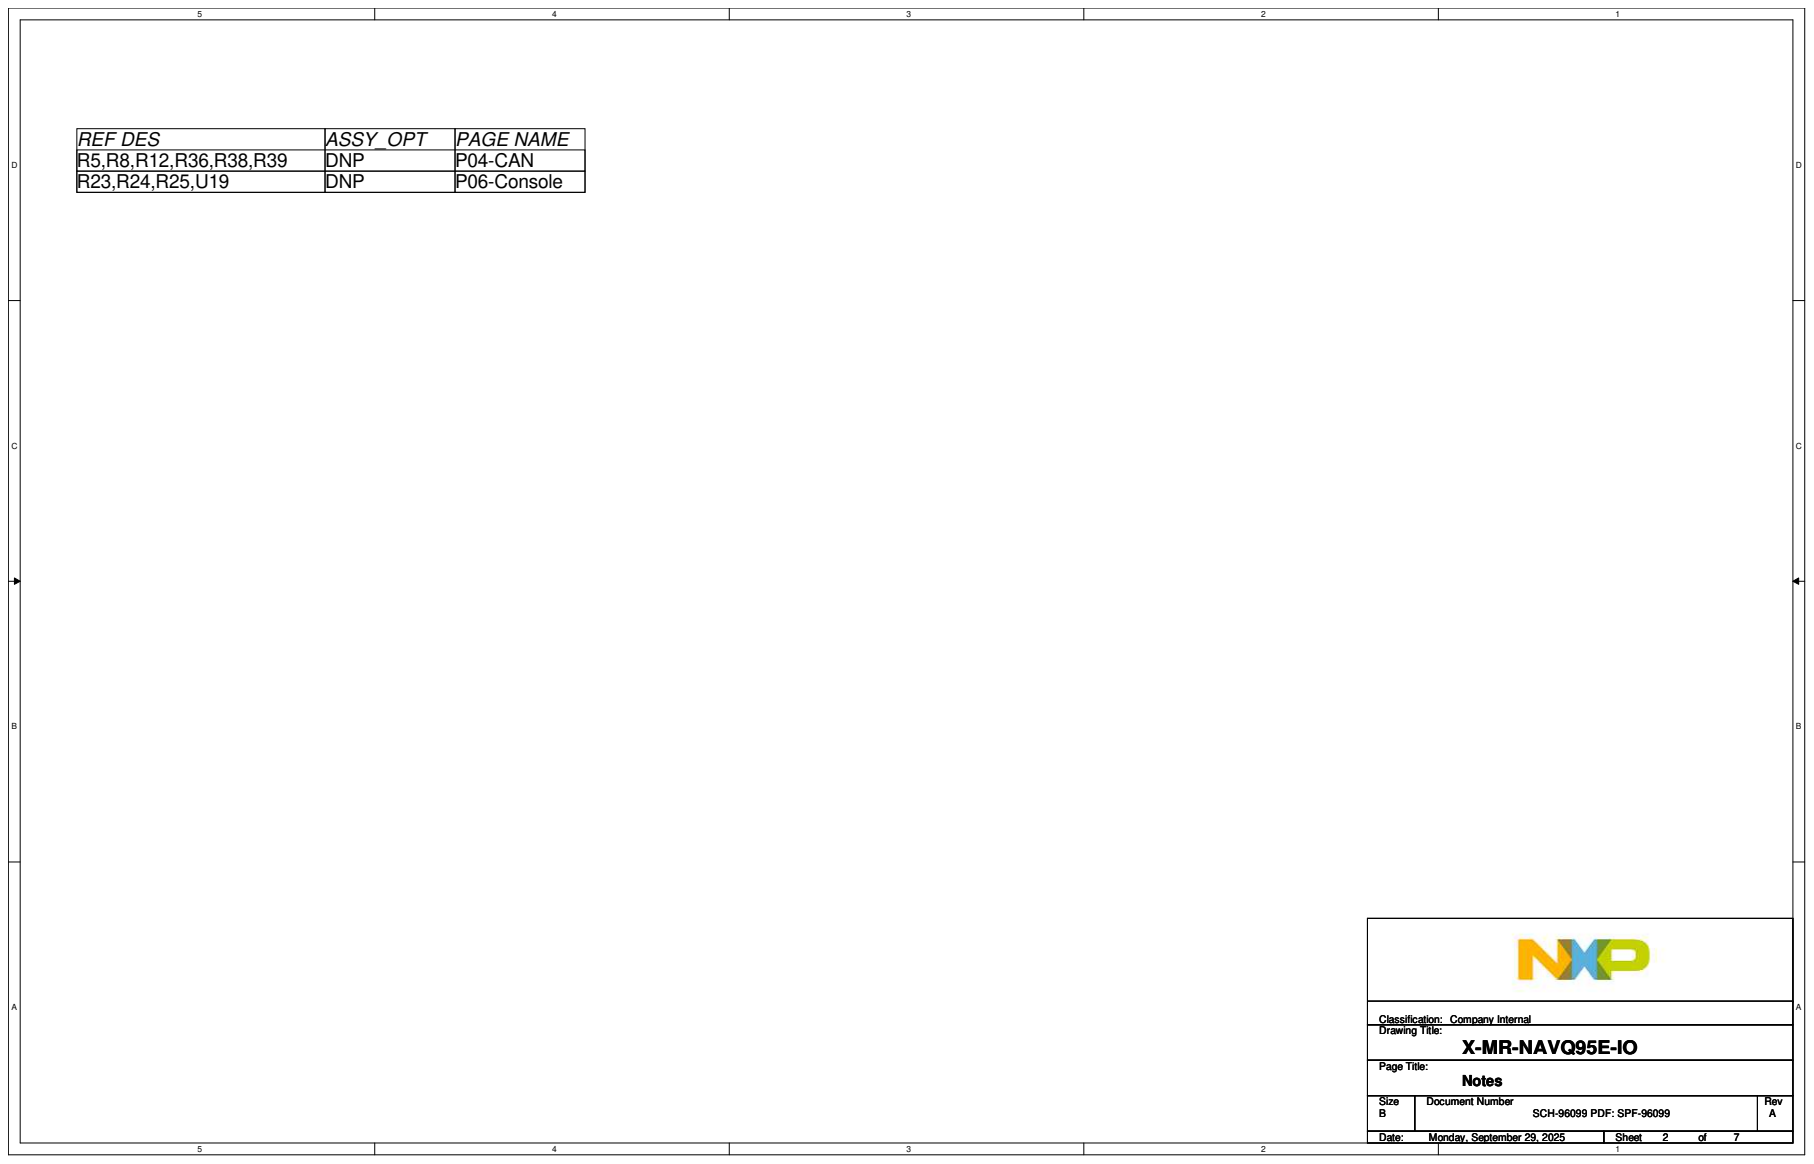
[picture p54: page 2]
DNP; P06-Console; Drawing Title:; Size; Document Number; Rev; Date:; Sheet; Page Title:; Classification:; SCH-96099 PDF: SPF-96099; X-MR-NAVQ95E-IO; Monday, September 29, 2025; Notes; Company Internal

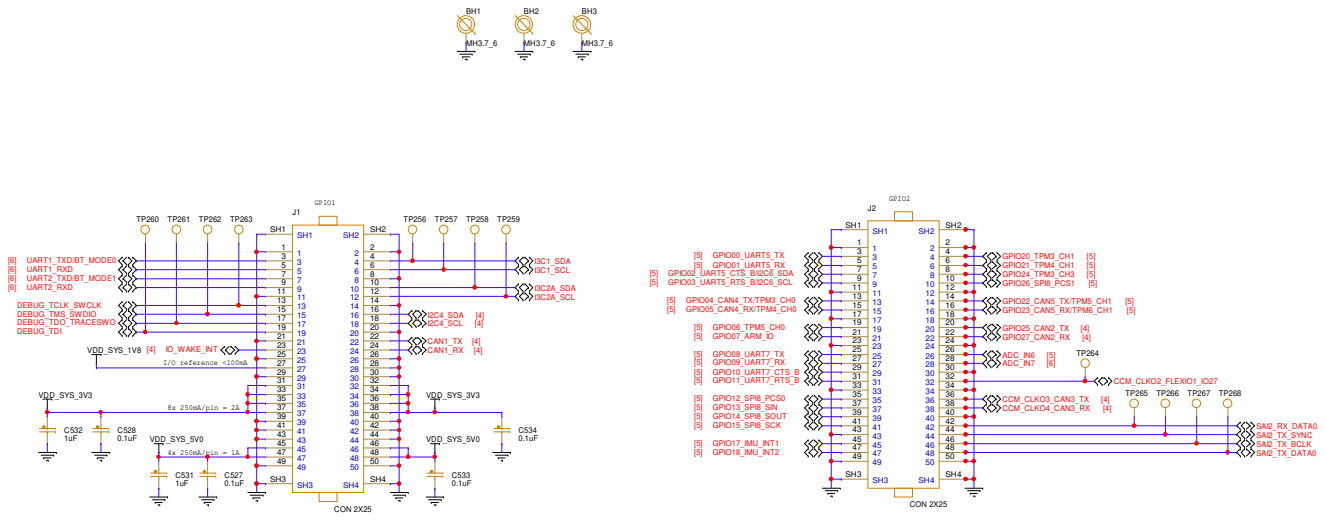
[picture p55: page 3]

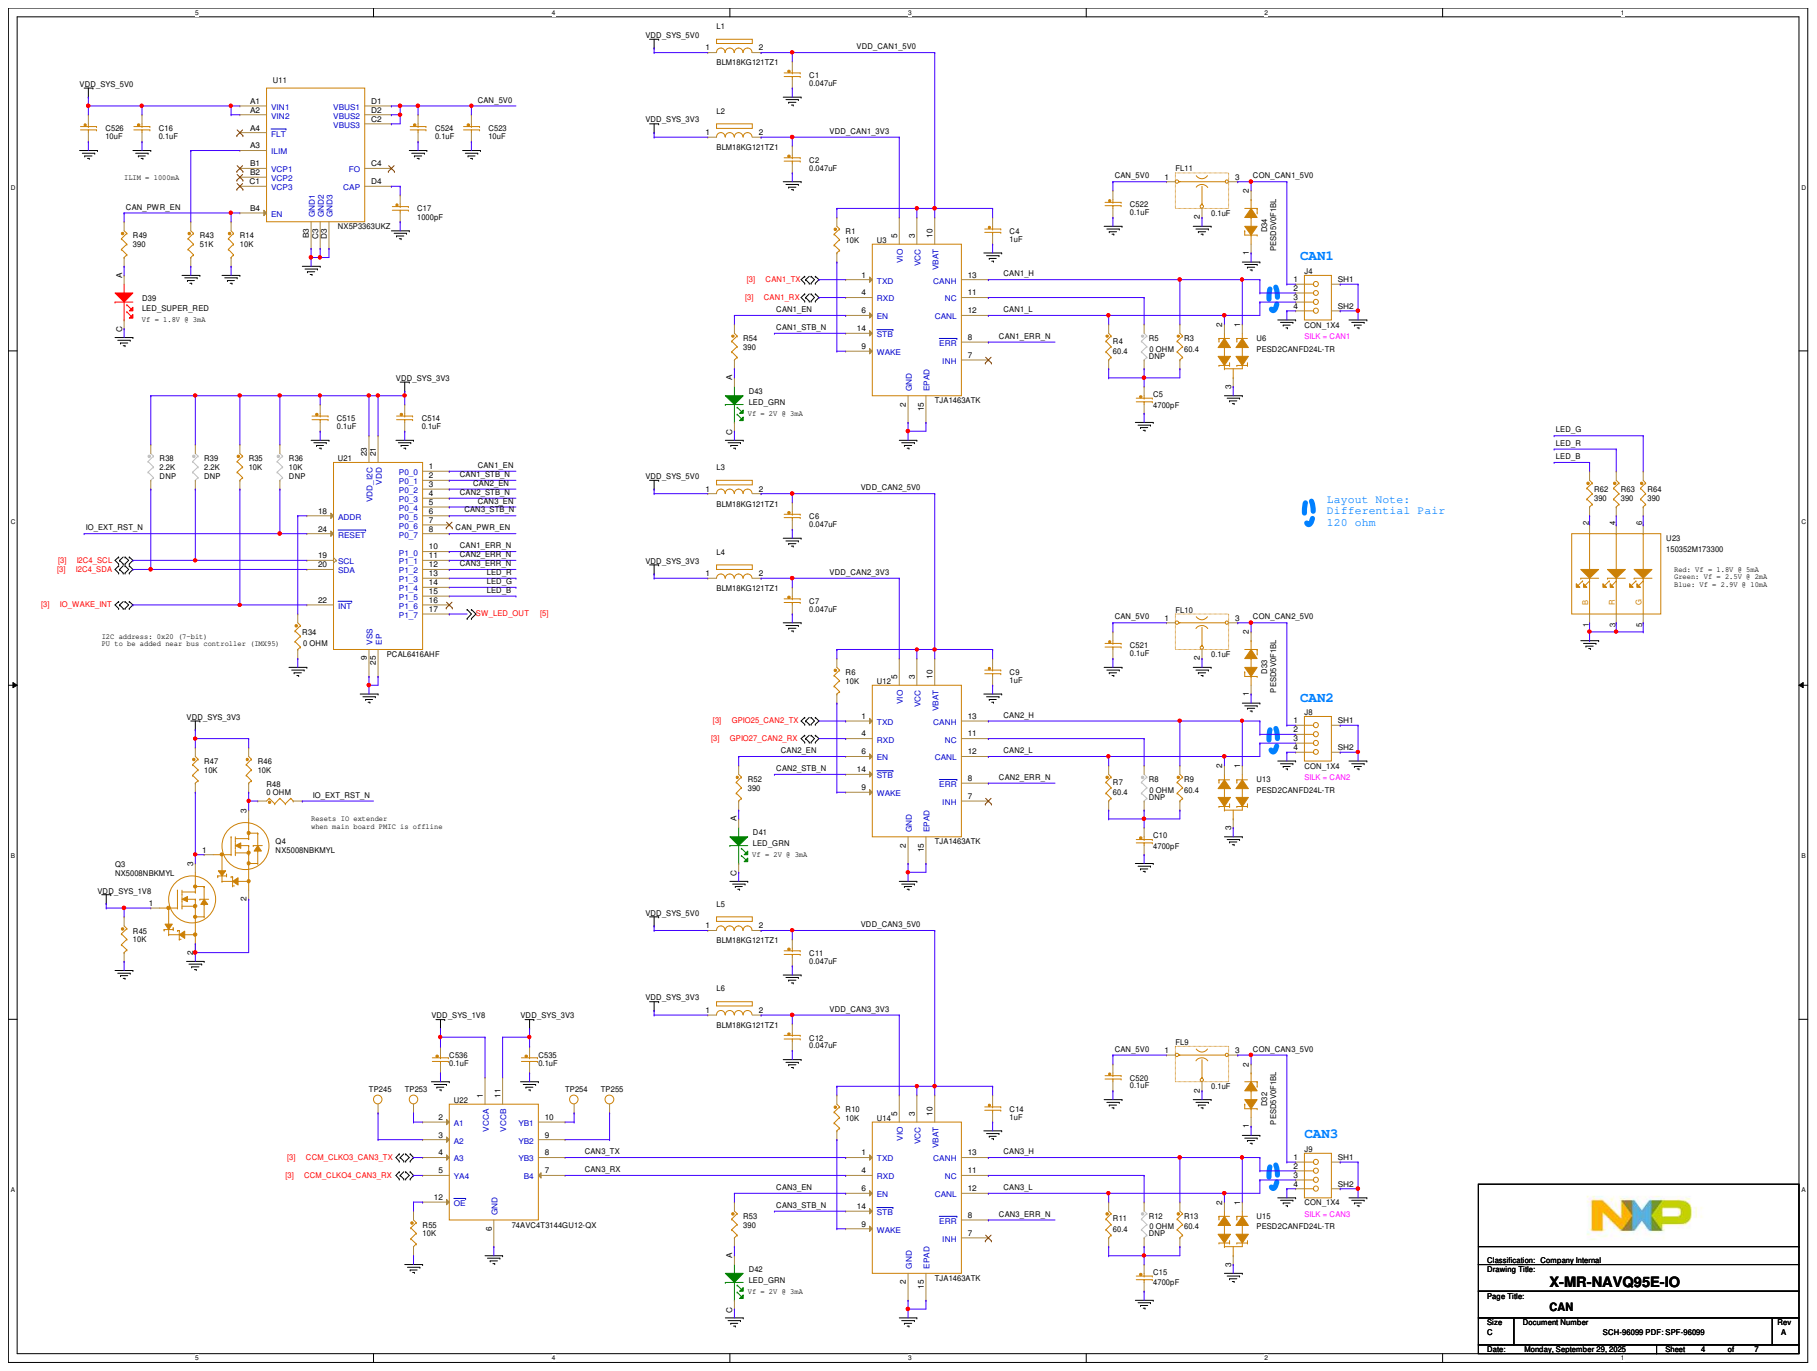
[picture p56: page 4]

I2C address: 0x20 (7-bit)
PU to be added near bus controller (IMX95)

Resets IO extender
when main board PMIC is offline

## MAX 12V on VDD_CON_PWM!

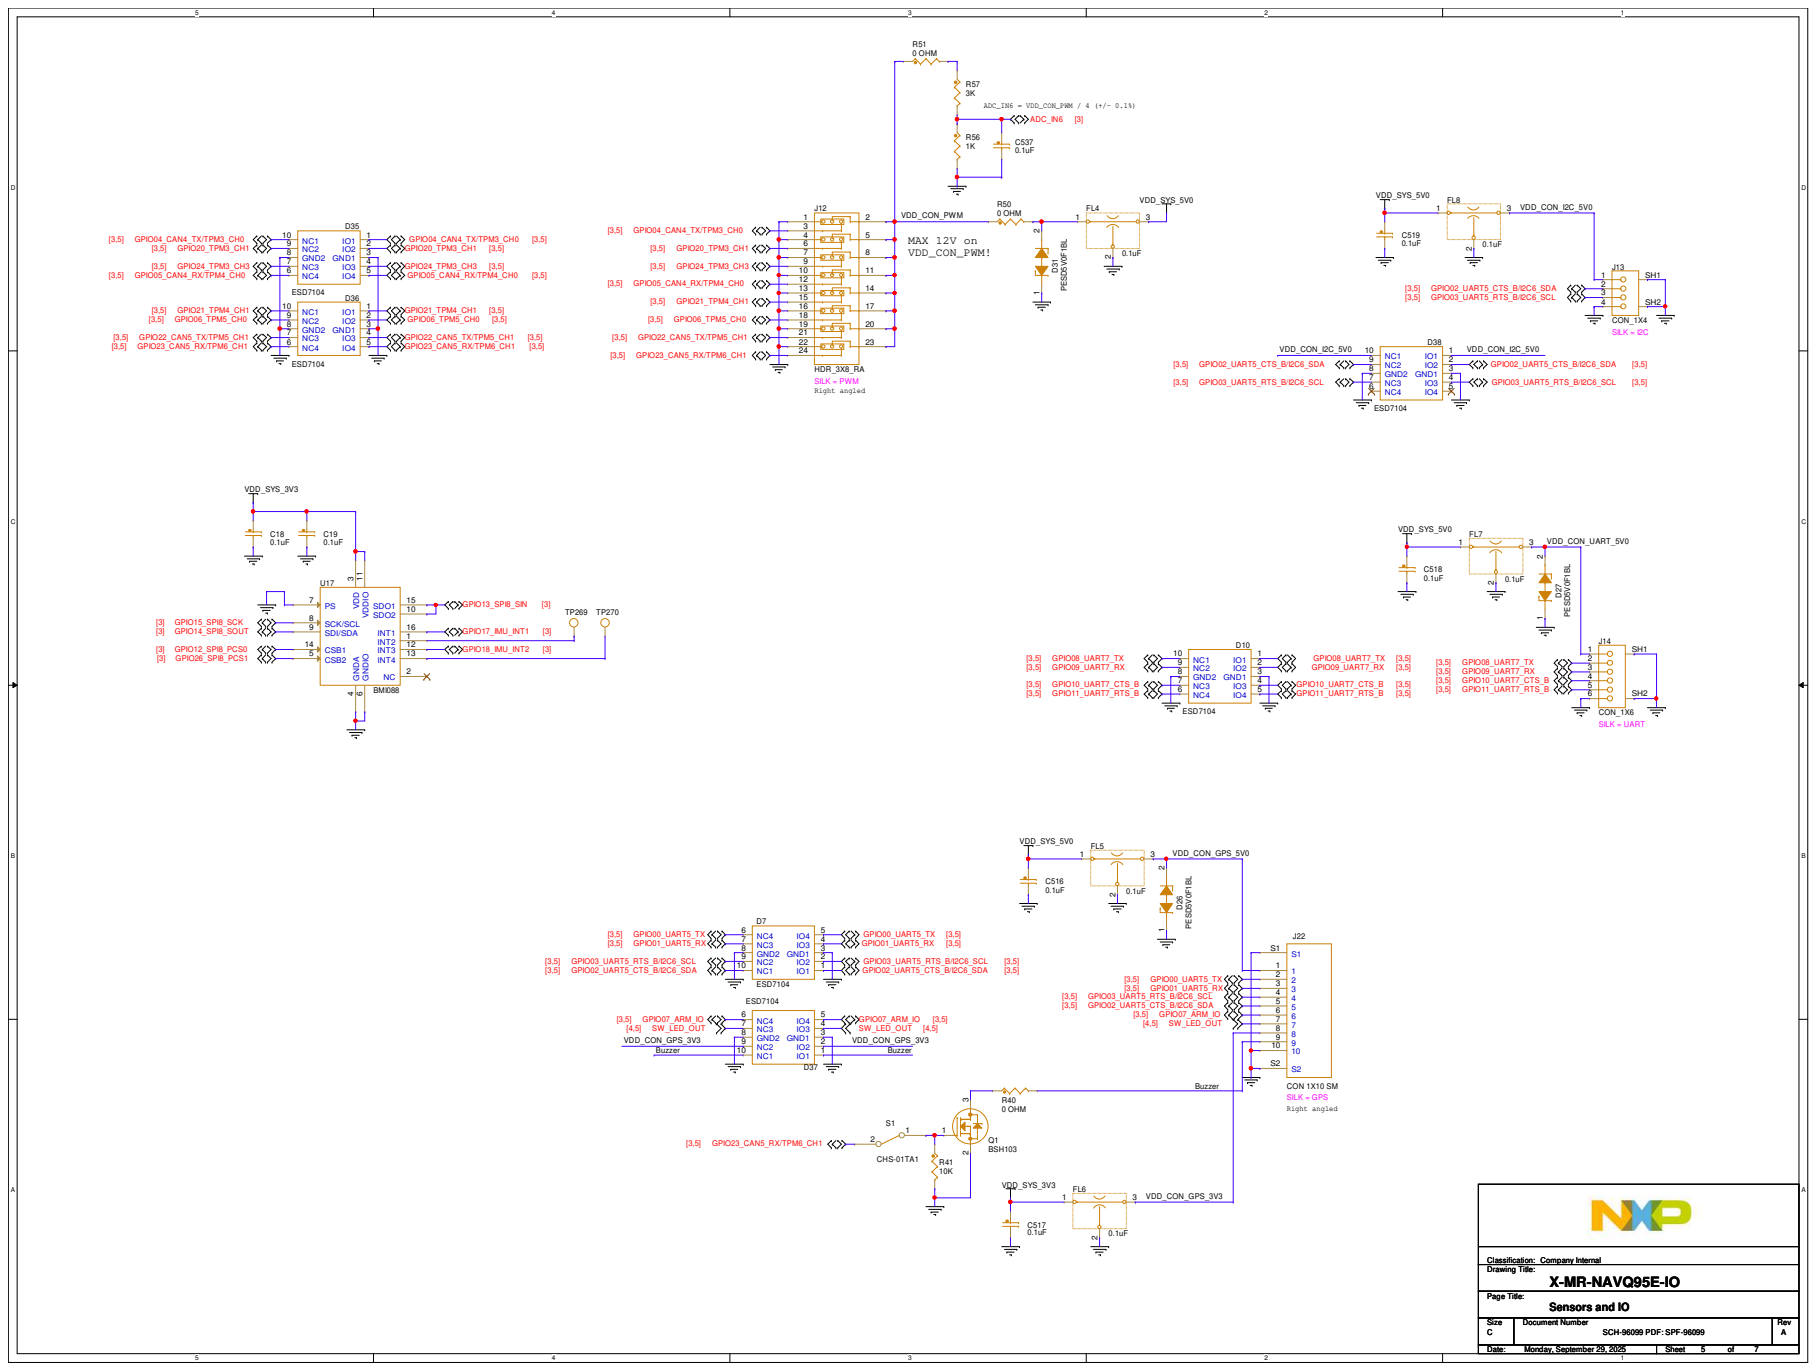
[picture p57: page 5]

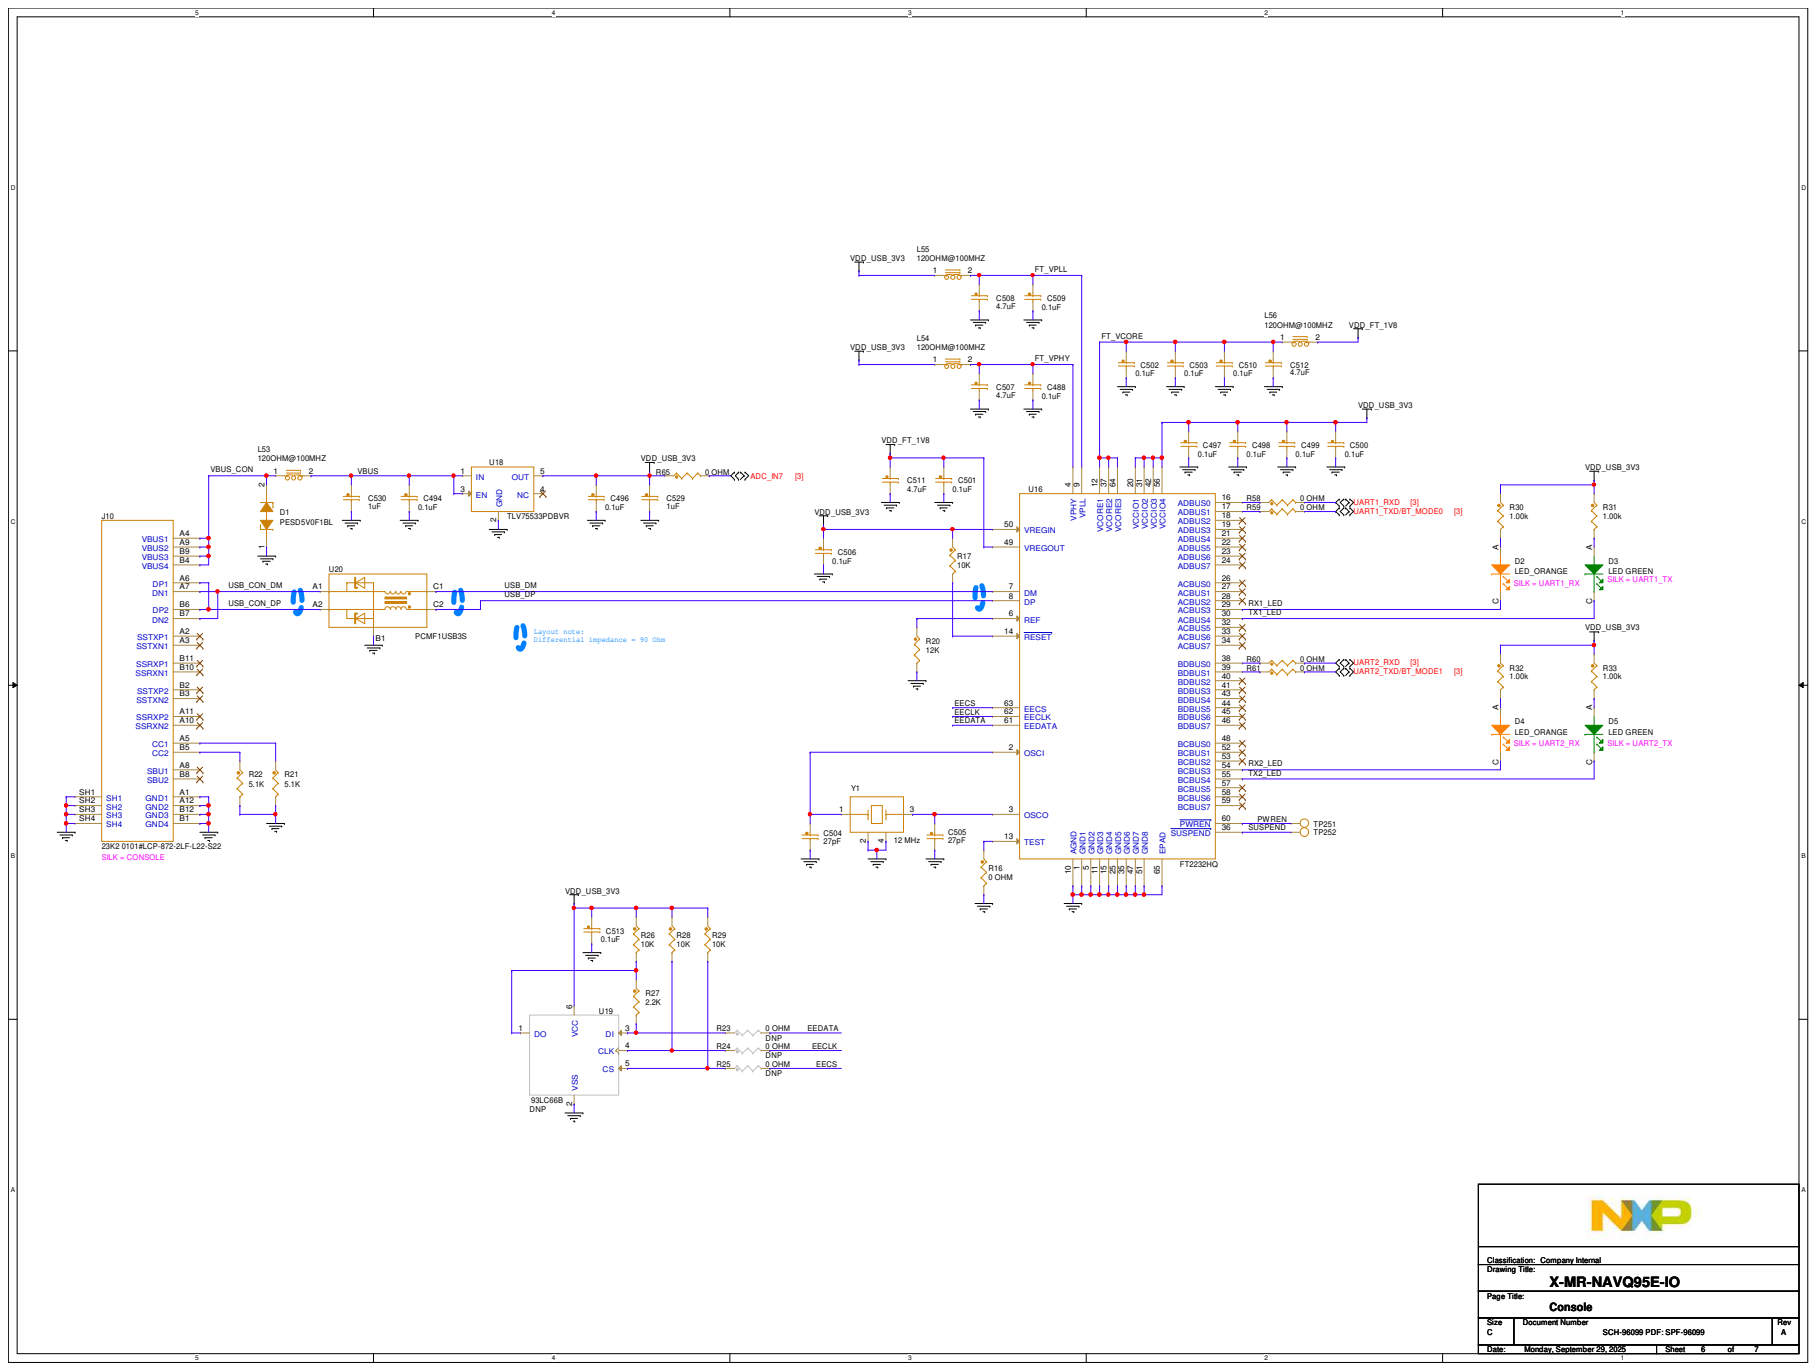
[picture p58: page 6]

# ByDate

2025-09-25

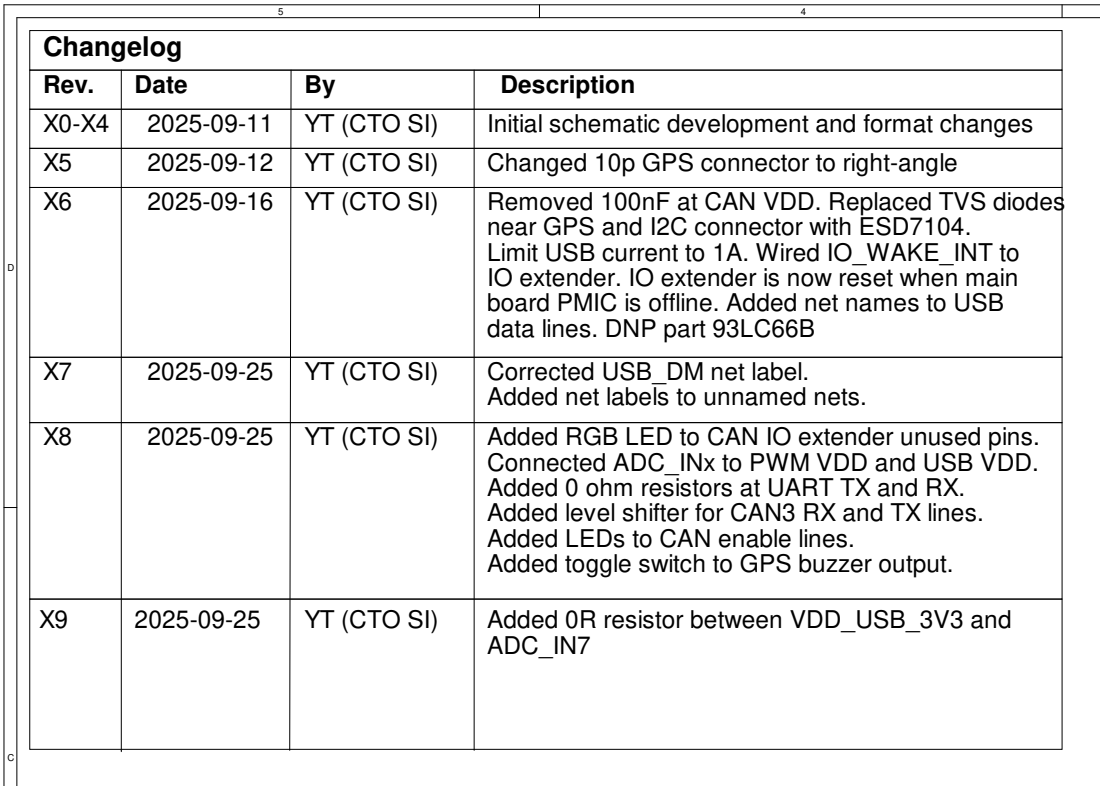
[picture p59: page 7]
(CTO SI); Initial schematic development and format changesYT; DescriptionRev.; Changelog; YT (CTO SI); Added 0R resistor between VDD_USB_3V3 and; ADC_IN7; Drawing Title:; Size; Document Number; Rev; Date:; Sheet; Page Title:; Classification:; SCH-96099 PDF: SPF-96099; X-MR-NAVQ95E-IO; Monday, September 29, 2025; Company Internal

YT (CTO SI)

Changed 10p GPS connector to right-angle
Removed 100nF at CAN VDD. Replaced TVS diodes
near GPS and I2C connector with ESD7104.
Limit USB current to 1A. Wired IO_WAKE_INT to
IO extender. IO extender is now reset when main
board PMIC is offline. Added net names to USB
data lines. DNP part 93LC66B
Corrected USB_DM net label.
Added net labels to unnamed nets.
Added RGB LED to CAN IO extender unused pins.
Connected ADC_INx to PWM VDD and USB VDD.
Added 0 ohm resistors at UART TX and RX.
Added level shifter for CAN3 RX and TX lines.
Added LEDs to CAN enable lines.
Added toggle switch to GPS buzzer output.

YT (CTO SI)X8
