NXP-Robotics/MR-NAVQ95/Schematic/Prototypes/Schematic-Rev-A/SPF-96100_A-CAM.pdf

5

4

3

2

1

D | D
C | C
B | B
A | A

# Revision History

# 4. Special signal usage:

By
2025-09-12

# 1. Interrupted lines coded with the same letter or

letter combinations are electrically connected.

# NOTES:

# 3. Greyed out components indicate

Do Not Populate (DNP) during assembly.

# YT (CTO SI)

_P and _N denote a differential signal.

_B denotes an active-low signal.

# X-MR-NAVQ95E-CAM

# 6. All SILK display properties will be in this color

# Description

X0-X6

# 7. All schematic annotations will be in this color

Rev.

# 5. Interpret diagram in accordance with American National Standards Institute specifications, current

revision, with the exception of logic block symbology.

# Initial schematic development and format changes

2. Device type number is for reference only. The number varies with the manufacturer.

# Date

# Table of Contents

# P01 Cover P02 Notes

P03 CSI to RPi | 2025-09-25 | YT (CTO SI)A | Schematic is released

# ChangelogP04

Drawing Title:

Size | Document Number | Rev
Date: | Sheet | of

Page Title:

Designer:

Drawn by:

Approved:

## System Innovation

High Tech Campus 60
5656 AG Eindhoven, The Netherlands This document contains information proprietary to NXP and shall not be used for engineering design, procurement or manufacture in whole or in part without the express written permission of NXP Semiconductors.
© | Classification:NXP SEMICONDUCTORS
SCH-96100 PDF: SPF-96100 | A

# X-MR-NAVQ95E-CAM

C

Monday, September 29, 2025

## Cover

Youri Tils

Jari van Ewijk

Youri Tils

1 | 4

Company Internal/Proprietary Drawing Title:

Size | Document Number | Rev
Date: | Sheet | of

Page Title:

Designer:

Drawn by:

Approved:

## System Innovation

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

# X-MR-NAVQ95E-CAM

C

Monday, September 29, 2025

## Cover

Youri Tils

Jari van Ewijk

Youri Tils

1 | 4

Company Internal/Proprietary Drawing Title:

Size | Document Number | Rev
Date: | Sheet | of

Page Title:

Designer:

Drawn by:

Approved:

## System Innovation

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

# X-MR-NAVQ95E-CAM

C

Monday, September 29, 2025

## Cover

Youri Tils

Jari van Ewijk

Youri Tils

1 | 4

Company Internal/Proprietary

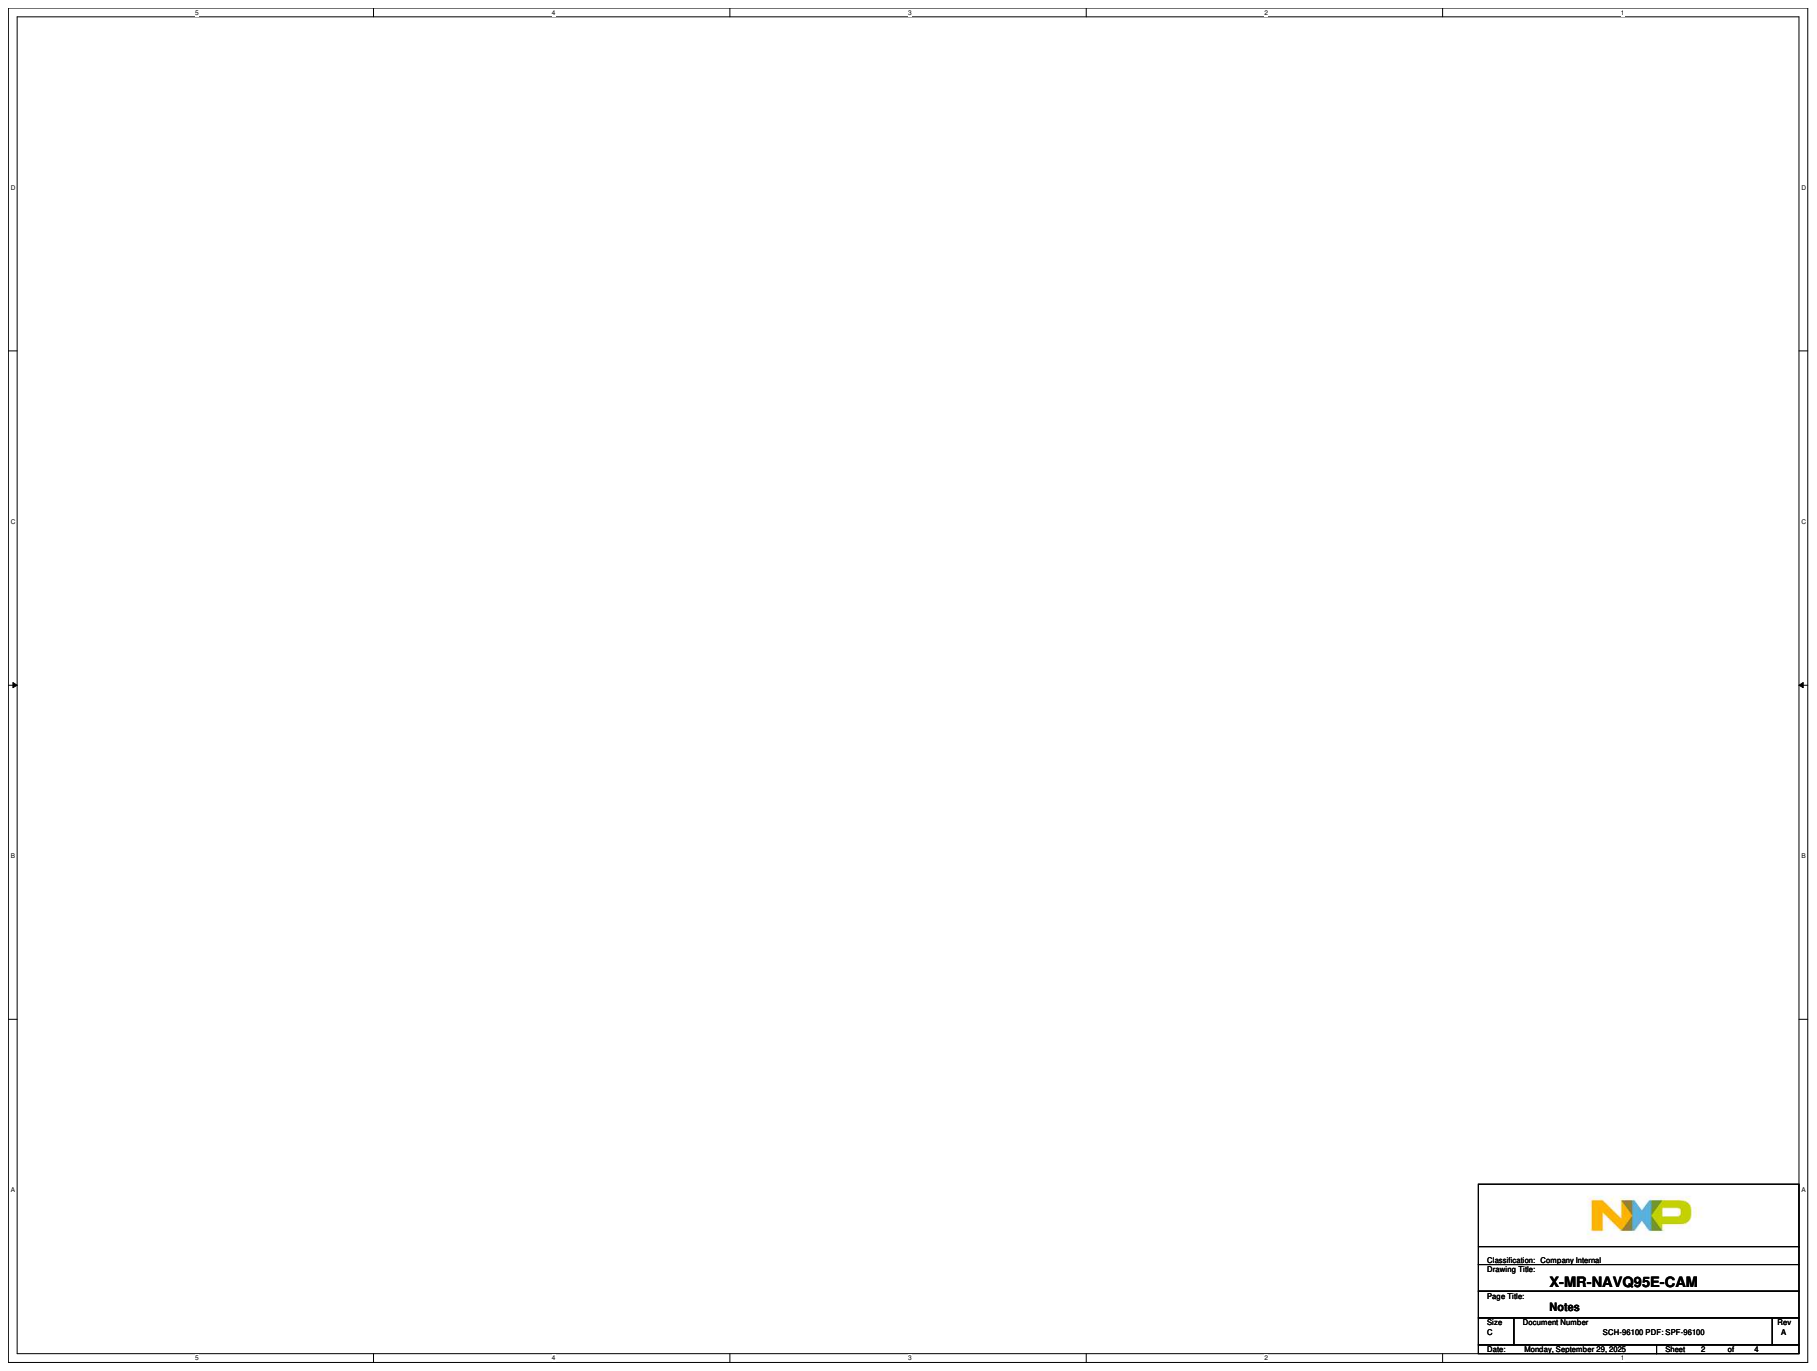
[picture p60: page 2]
Drawing Title:; Size; Document Number; Rev; Date:; Sheet; Page Title:; Classification:; SCH-96100 PDF: SPF-96100; X-MR-NAVQ95E-CAM; Monday, September 29, 2025; Notes; Company Internal

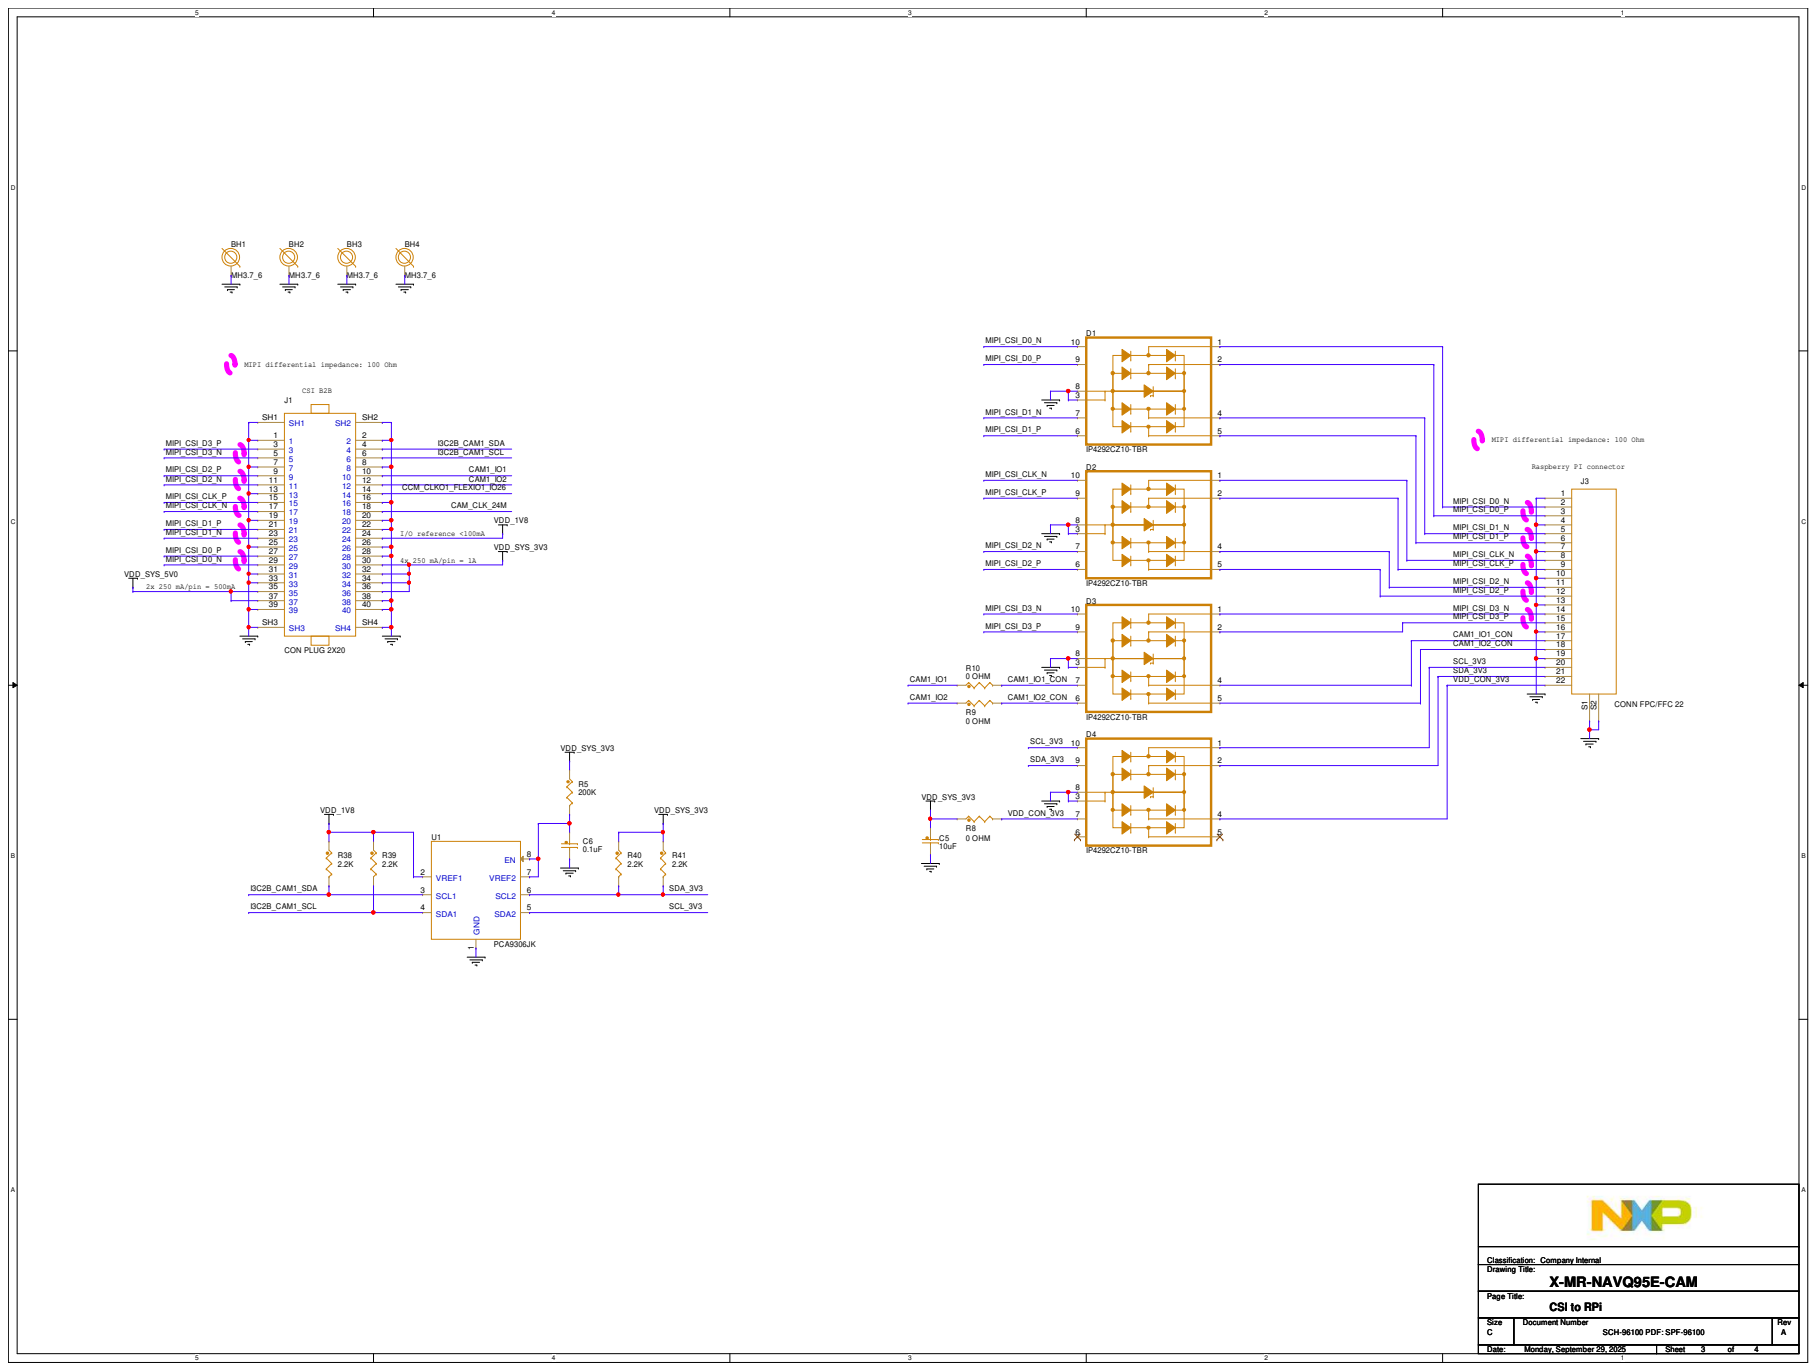
[picture p61: page 3]

MIPI differential impedance: 100 Ohm

Rev.

# Initial schematic development and format changes

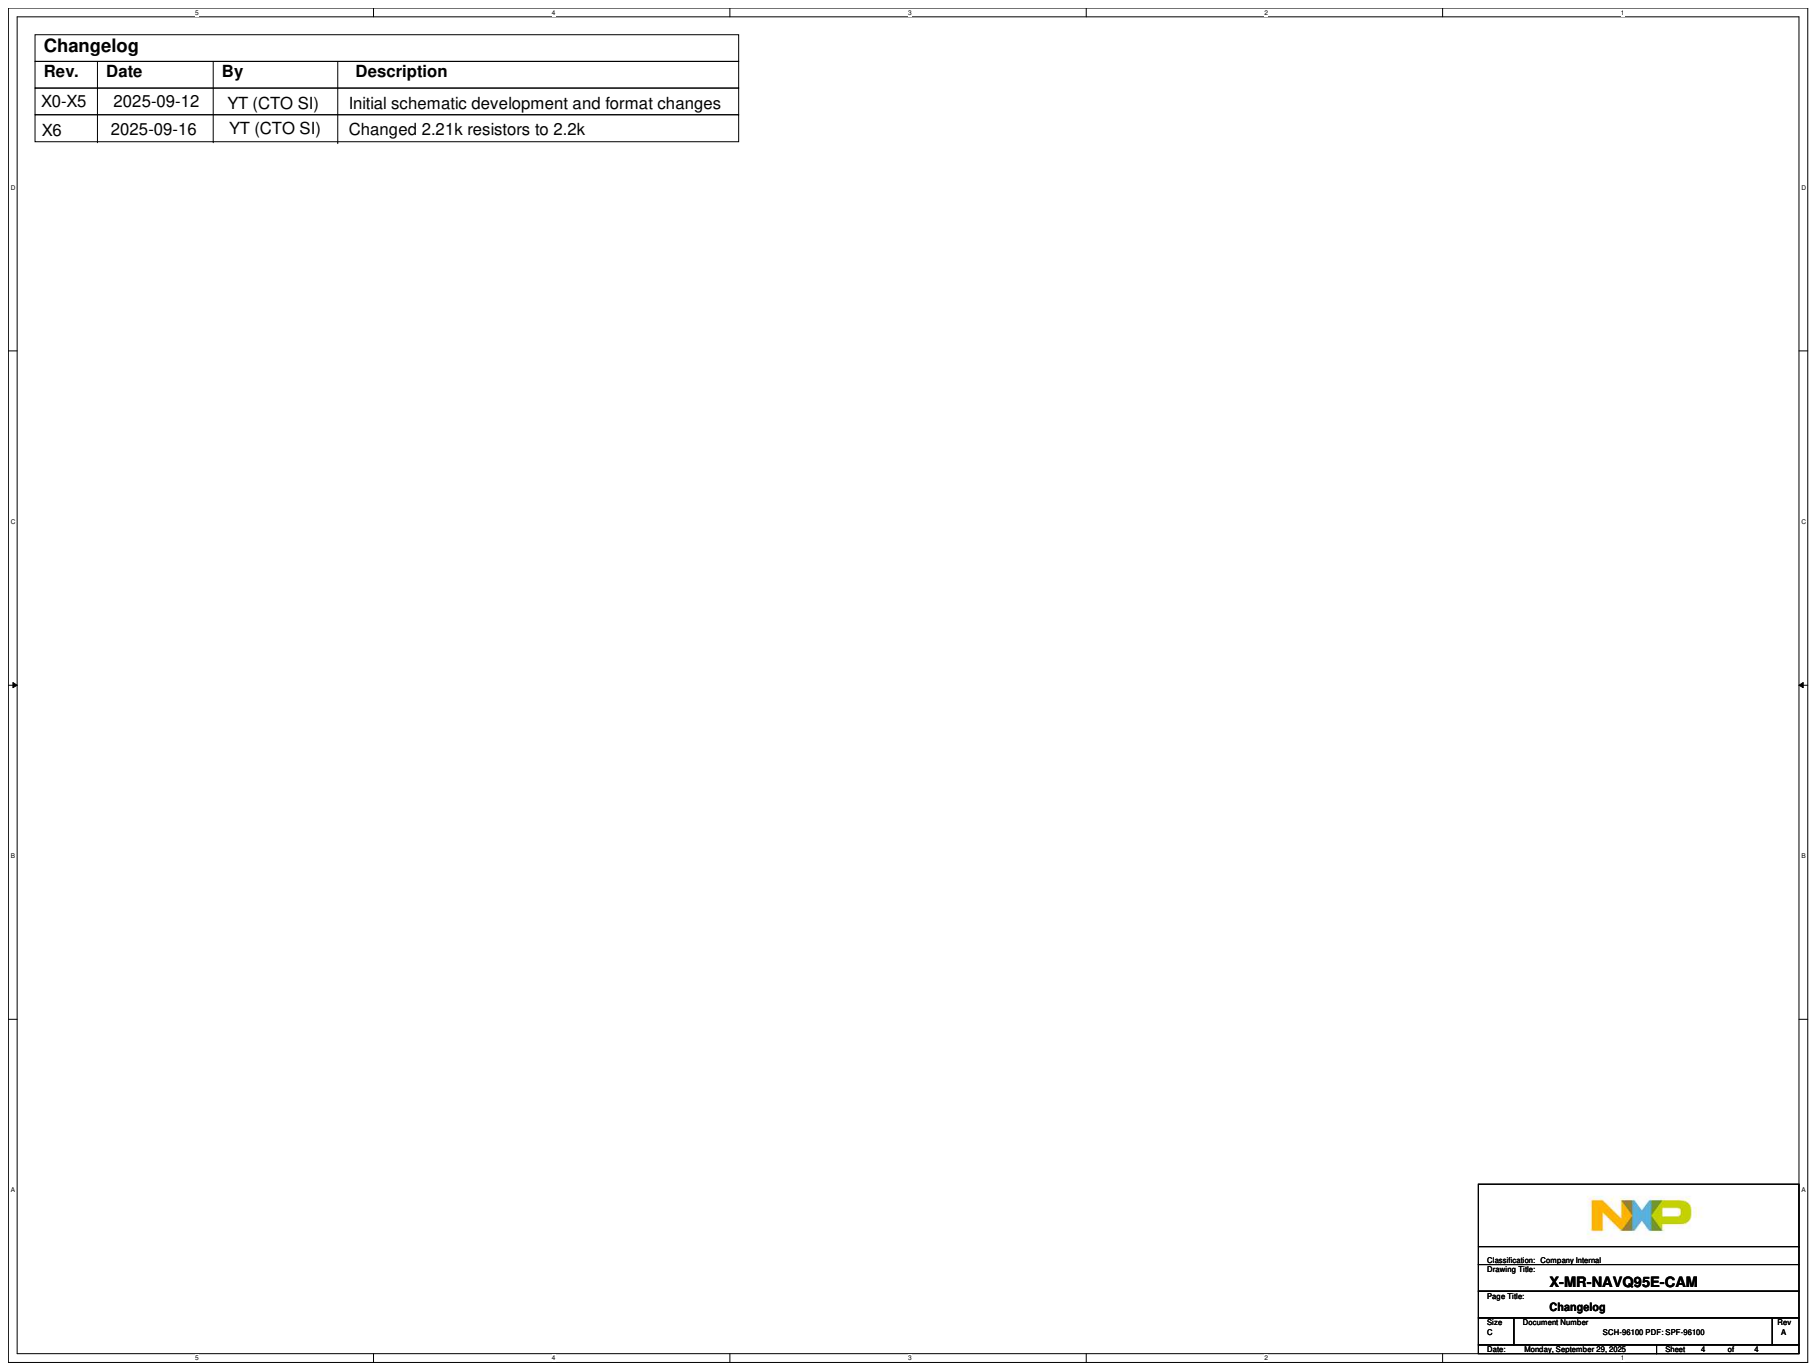
[picture p62: page 4]
Changelog; Changed 2.21k resistors to 2.2k2025-09-16; Description; Date; Drawing Title:; Size; Document Number; Rev; Date:; Sheet; Page Title:; Classification:; SCH-96100 PDF: SPF-96100; X-MR-NAVQ95E-CAM; Monday, September 29, 2025; Company Internal

YT (CTO SI)
