NXP-Robotics/MR-NAVQ95/Schematic/Prototypes/Schematic-Rev-A/SPF-96101_A-T1SWITCH.pdf

5

4

3

2

1

D | D
C | C
B | B
A | A

# Table of Contents

# P01 Cover P02 Notes P03 ETH_POWER_PF5103 P04 ETH_SJA1110_SUPPLY P05 ETH_SJA1110_DATA P06 ETH_100BASET1_MDIs P07 ETH_TJA1120_1 P08 ETH_TJA1120_2 P09 ETH_B2B

By

# YT (CTO SI) Schematic is released Description

2025-09-29A

# Rev. Date

# Revision History

2. Device type number is for reference only. The number varies with the manufacturer.

# 5. Interpret diagram in accordance with American National Standards Institute specifications, current

revision, with the exception of logic block symbology.

# NOTES:

# 4. Special signal usage:

# 3. Greyed out components indicate

Do Not Populate (DNP) during assembly.

_P and _N denote a differential signal.

# 6. All SILK display properties will be in this color

_B denotes an active-low signal.

# 1. Interrupted lines coded with the same letter or

letter combinations are electrically connected.

# 7. All schematic annotations will be in this color

# X-MR-NAVQ95E-T1S

X0-X9 | 2025-09-11 | YT (CTO SI) | Initial schematic development and format changes

# ChangelogP10

Drawing Title:

Size | Document Number | Rev
Date: | Sheet | of

Page Title:

Designer:

Drawn by:

Approved:

## System Innovation

High Tech Campus 60
5656 AG Eindhoven, The Netherlands This document contains information proprietary to NXP and shall not be used for engineering design, procurement or manufacture in whole or in part without the express written permission of NXP Semiconductors.
© | Classification:NXP SEMICONDUCTORS
SCH-96101 PDF: SPF-96101 | A

# X-MR-NAVQ95E-T1S

C

Monday, September 29, 2025

## Cover

Youri Tils

Jari van Ewijk

Youri Tils

1 | 10

Company Internal/Proprietary Drawing Title:

Size | Document Number | Rev
Date: | Sheet | of

Page Title:

Designer:

Drawn by:

Approved:

## System Innovation

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

# X-MR-NAVQ95E-T1S

C

Monday, September 29, 2025

## Cover

Youri Tils

Jari van Ewijk

Youri Tils

1 | 10

Company Internal/Proprietary Drawing Title:

Size | Document Number | Rev
Date: | Sheet | of

Page Title:

Designer:

Drawn by:

Approved:

## System Innovation

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

# X-MR-NAVQ95E-T1S

C

Monday, September 29, 2025

## Cover

Youri Tils

Jari van Ewijk

Youri Tils

1 | 10

Company Internal/Proprietary

REF DES | ASSY_OPT | PAGE NAME
R567,R568,R569,R581,R582, R584,R585,R586 | DNP | P03-ETH_POWER_PF5103

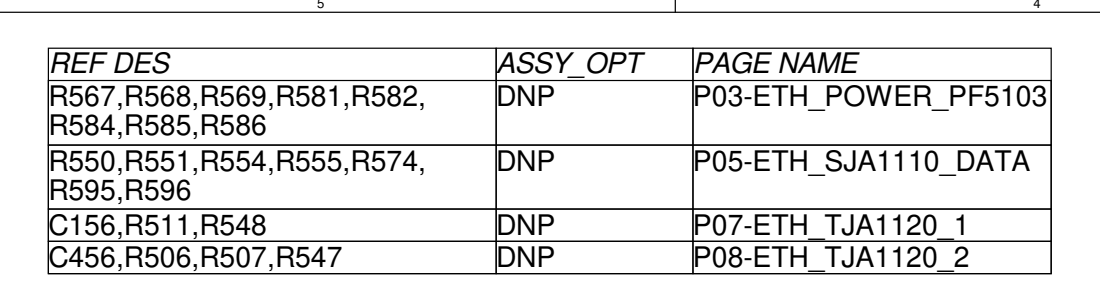
[picture p63: page 2]
Drawing Title:; Size; Document Number; Rev; Date:; Sheet; Page Title:; Classification:; SCH-96101 PDF: SPF-96101; X-MR-NAVQ95E-T1S; Monday, September 29, 2025; Notes; Company Internal

R550,R551,R554,R555,R574, R595,R596 | DNP | P05-ETH_SJA1110_DATA

C156,R511,R548 | DNP | P07-ETH_TJA1120_1
C456,R506,R507,R547 | DNP | P08-ETH_TJA1120_2

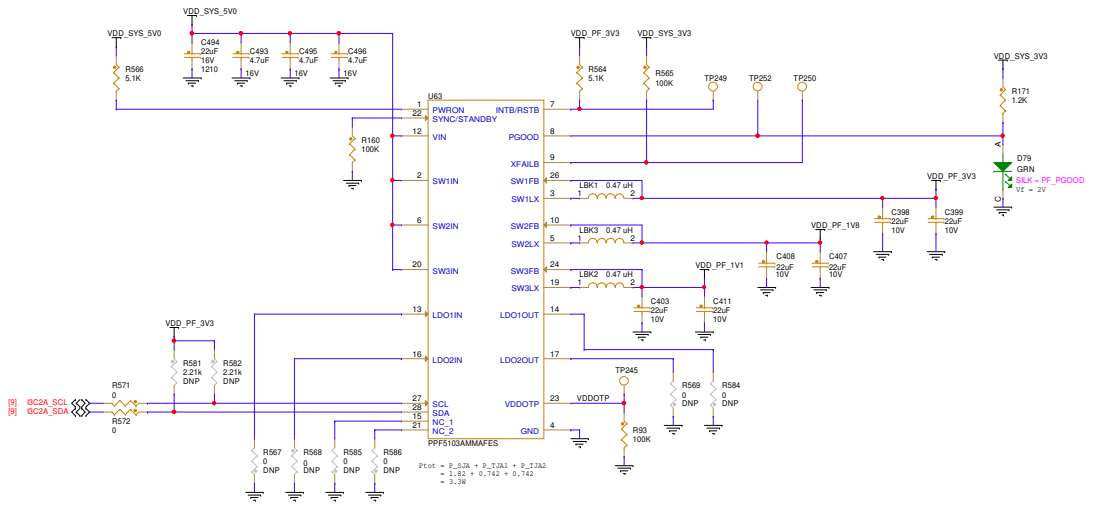
[picture p64: page 3]

# LDO output

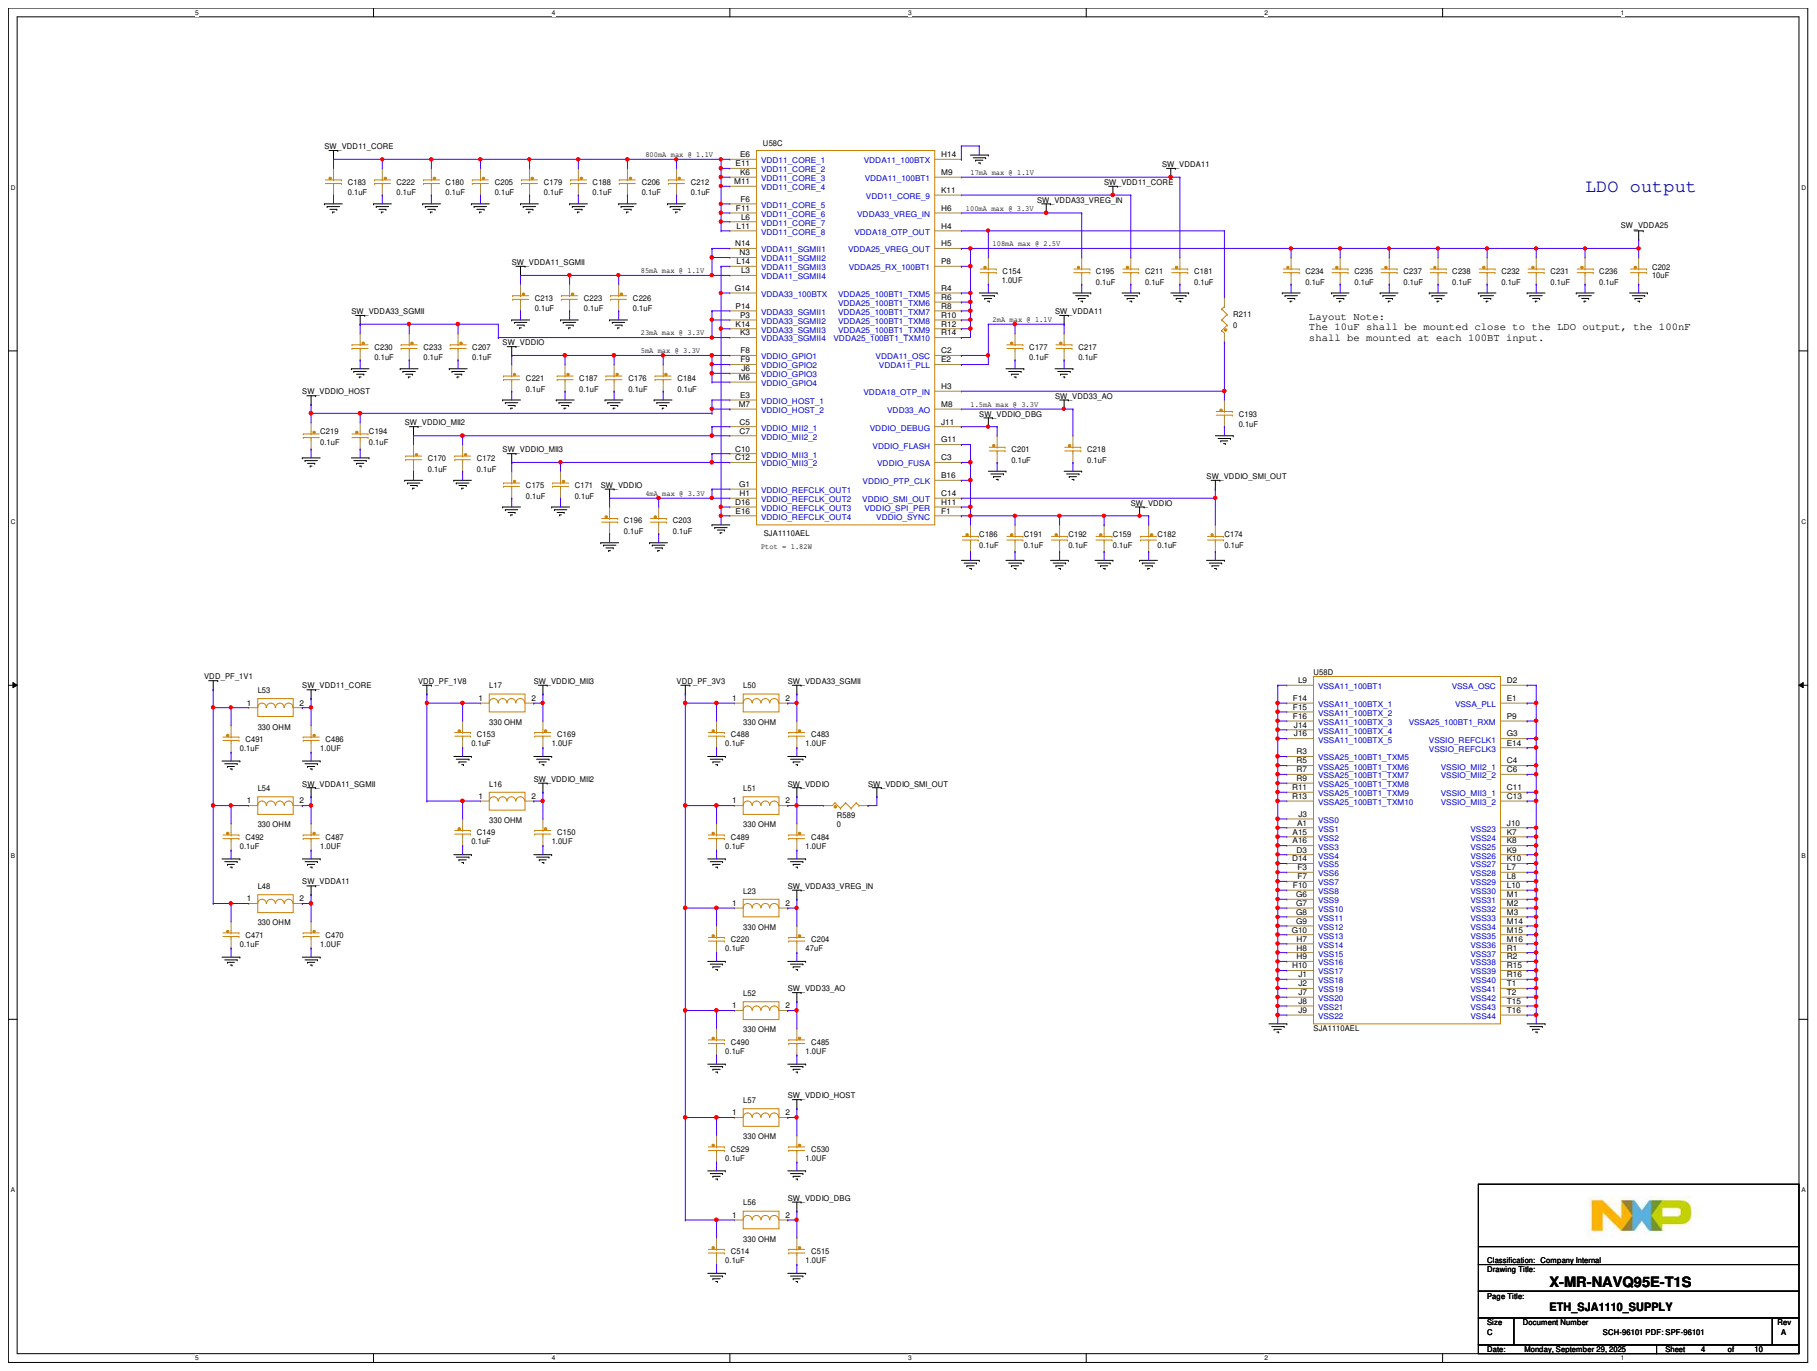
[picture p65: page 4]

Layout Note:
The 10uF shall be mounted close to the LDO output, the 100nF
shall be mounted at each 100BT input.

## Layout Note: Differential Pair

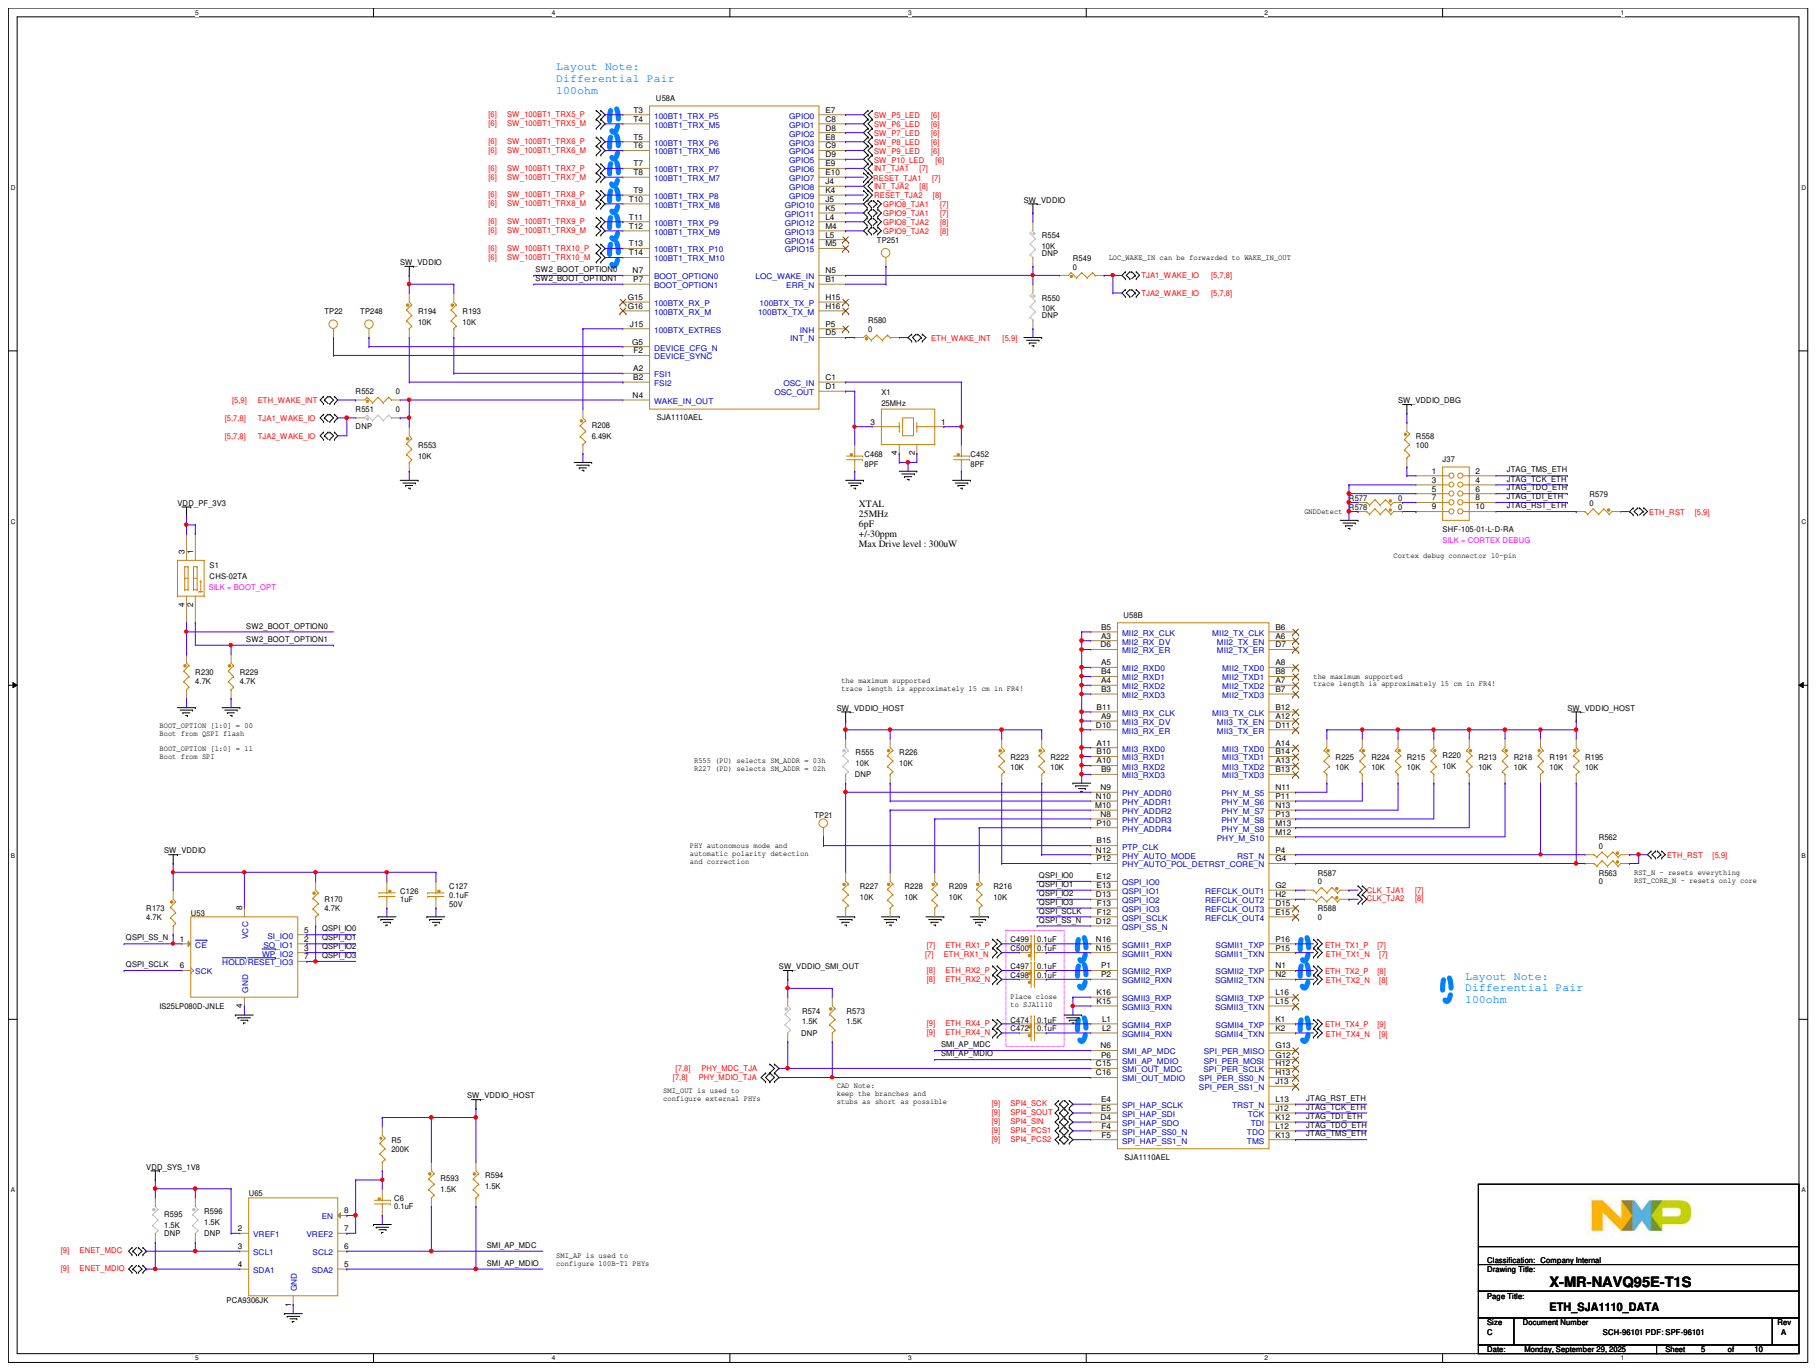
[picture p66: page 5]

LOC_WAKE_IN can be forwarded to WAKE_IN_OUT

Cortex debug connector 10-pin

the maximum supported
trace length is approximately 15 cm in FR4!

BOOT_OPTION [1:0] = 00
Boot from QSPI flash

N8
P10

PHY autonomous mode and
automatic polarity detection
and correction

CAD Note:
keep the branches and
stubs as short as possible

# 100BASE⁻T1 MDIs

## CAD Note:

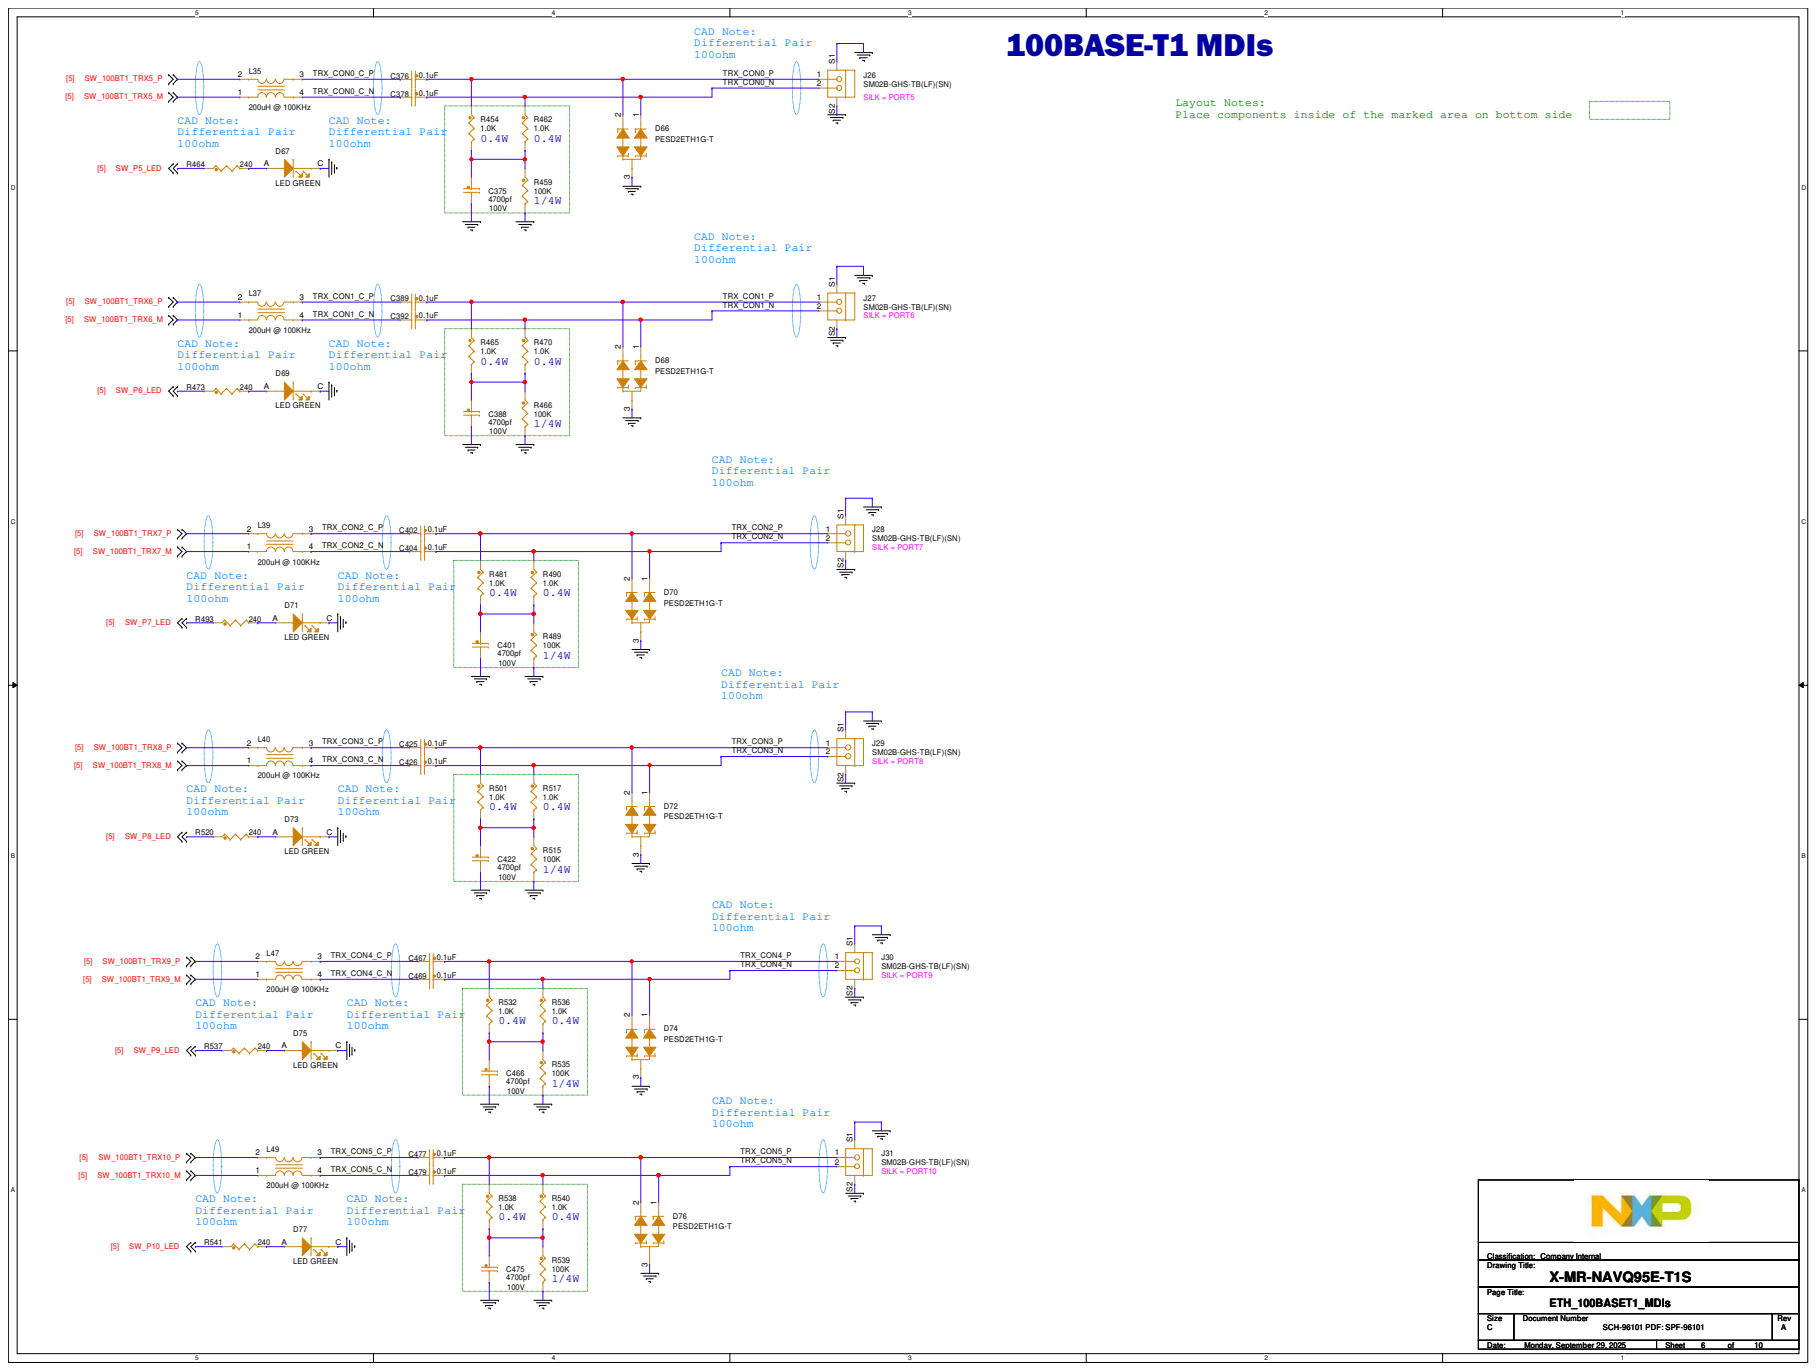
[picture p67: page 6]

Layout Notes:
Place components inside of the marked area on bottom side

# TJA1

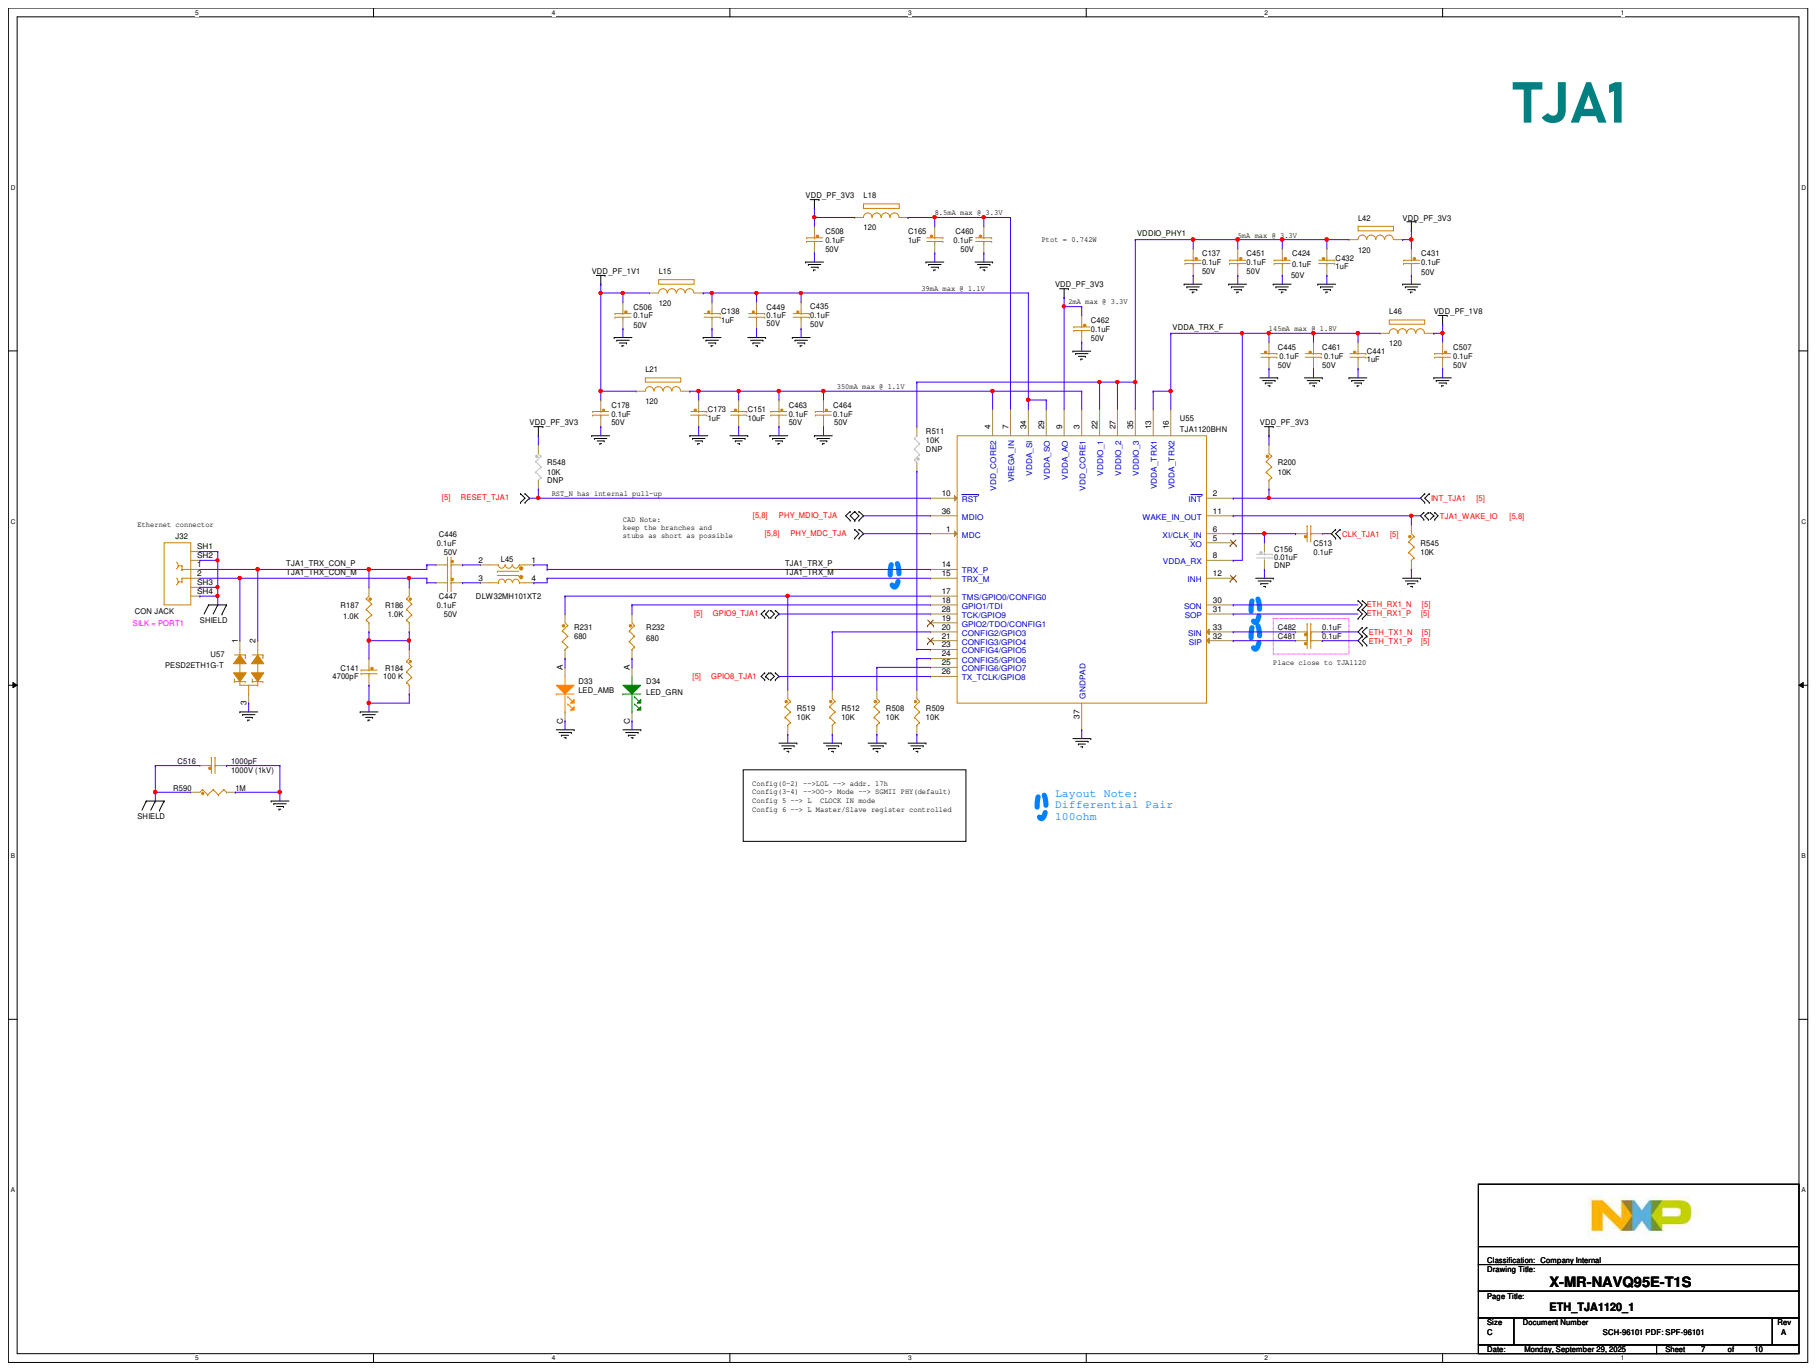
[picture p68: page 7]

RST_N has internal pull-up

CAD Note:
keep the branches and
stubs as short as possible

Config(0-2) -->LOL --> addr. 17h
Config(3-4) -->OO-> Mode --> SGMII PHY(default)
Config 6 --> L Master/Slave register controlled

# TJA2

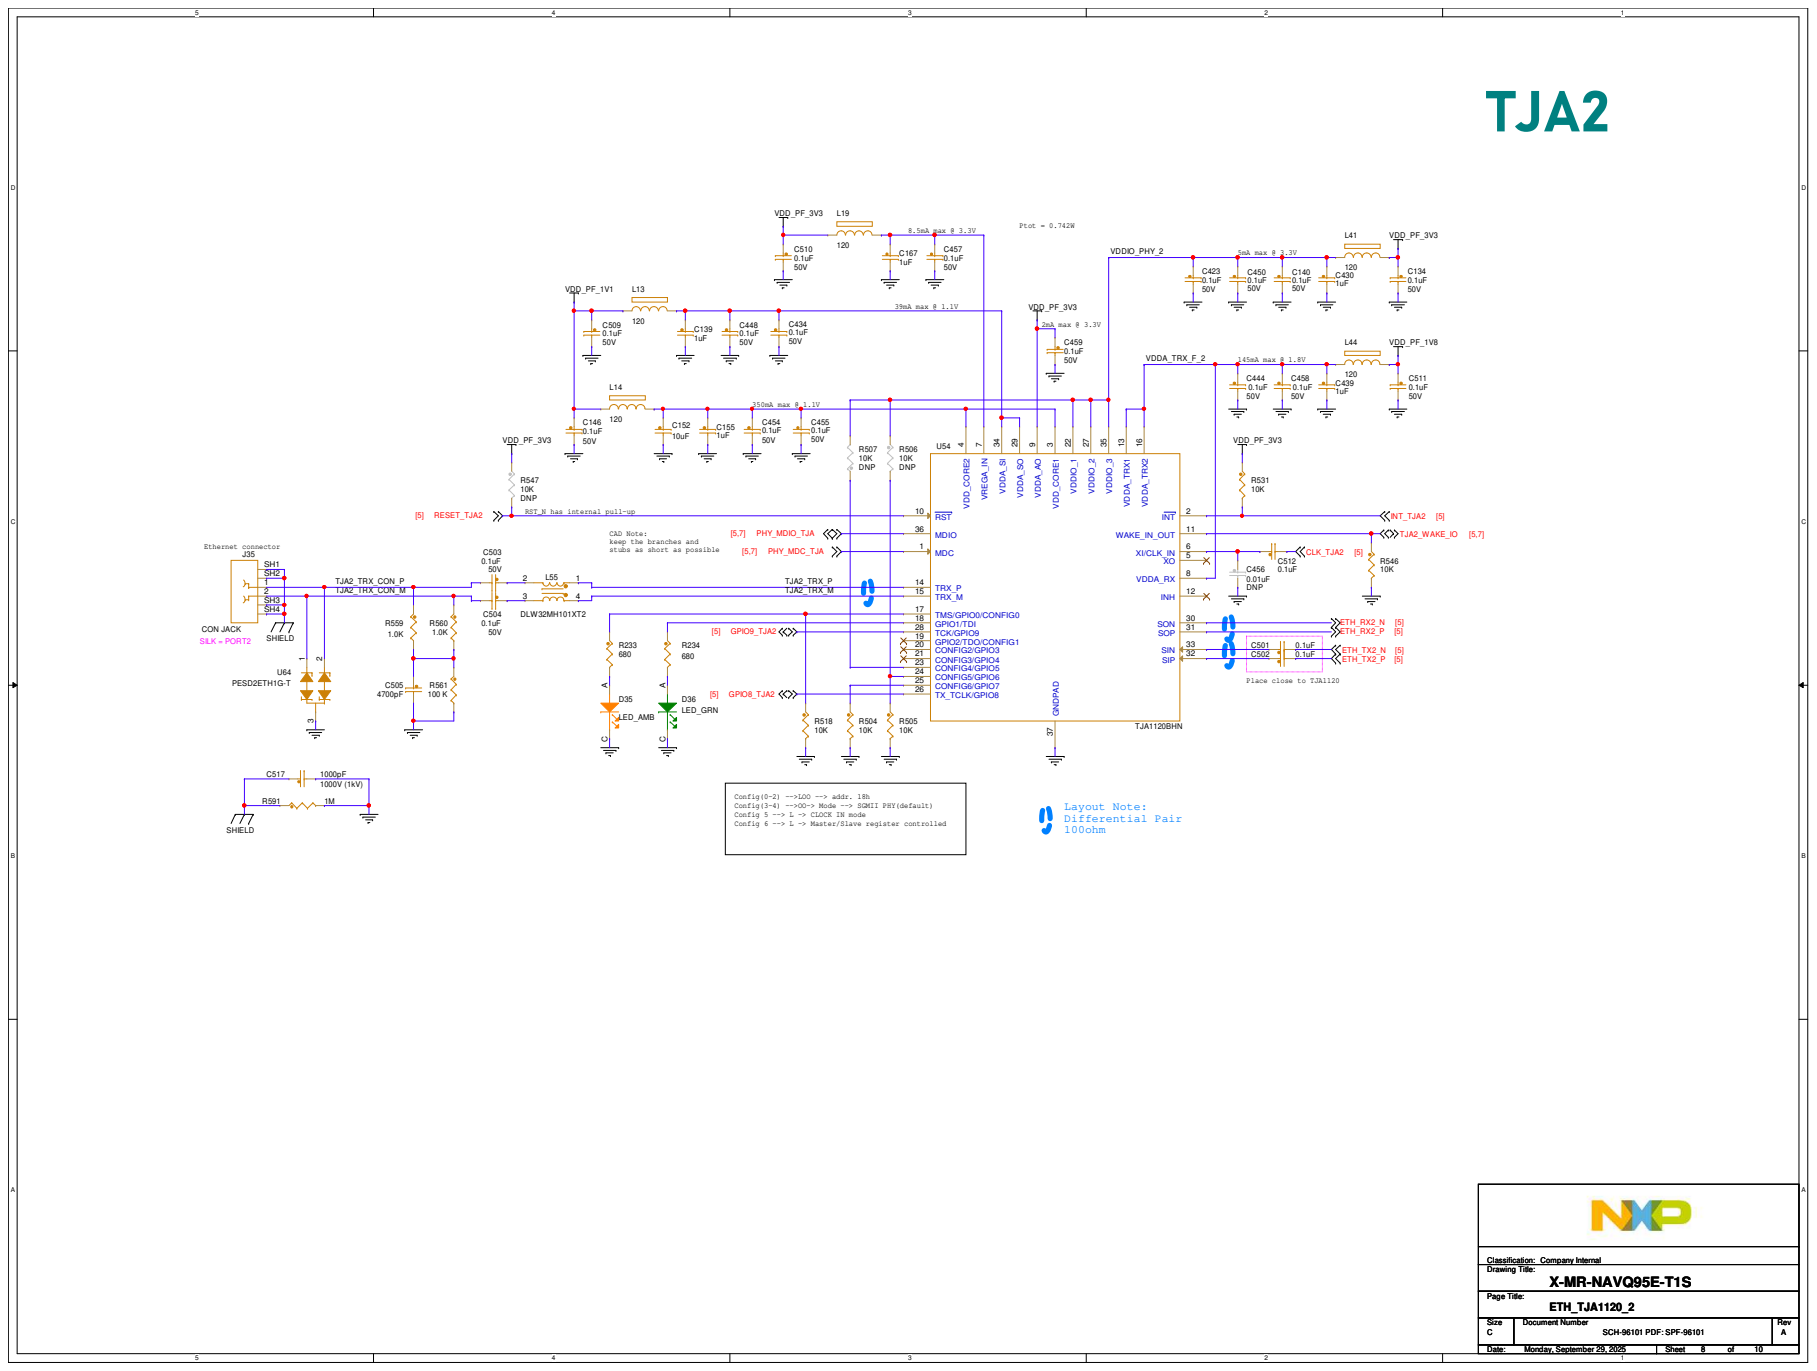
[picture p69: page 8]

RST_N has internal pull-up

CAD Note:
keep the branches and
stubs as short as possible

Config(0-2) -->LOO --> addr. 18h
Config(3-4) -->OO-> Mode --> SGMII PHY(default)
Config 5 --> L -> CLOCK IN mode
Config 6 --> L -> Master/Slave register controlled

8x 250mA/pin = 2A; 4x 250mA/pin = 1A; I/O reference <100mA; Layout Note: Differential Pair 100ohm; VDD_SYS_5V0; VDD_SYS_3V3; VDD_SYS_1V8; ETH_TX4_P; ETH_TX4_N; ETH_RX4_P; ETH_RX4_N; SPI4_SOUT[5] SPI4_SIN[5] SPI4_SCK[5] SPI4_PCS1[5] SPI4_PCS2[5]; I3C2A_SDA[3] I3C2A_SCL[3]; ENET_MDIO[5] ENET_MDC[5]; ETH_WAKE_INT; ETH_RST; Drawing Title:; Size; Document Number; Rev; Date:; Sheet; Page Title:; Classification:; SCH-96101 PDF: SPF-96101; X-MR-NAVQ95E-T1S; Monday, September 29, 2025; ETH_B2B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

# Added correct shielding circuit to ethernet connectors and power consumption information

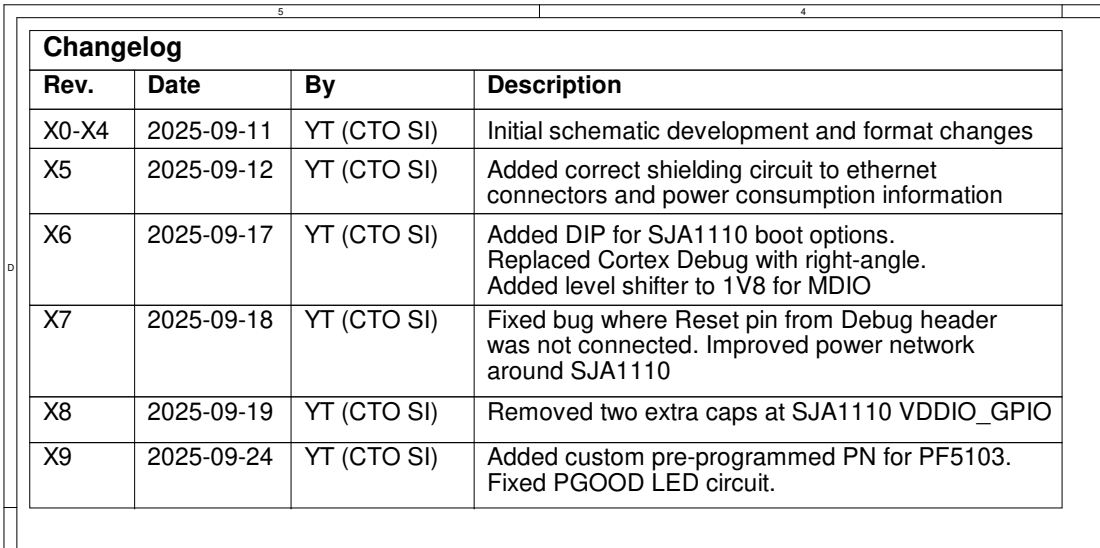
[picture p70: page 10]
Changelog; Rev.; DescriptionByDate; YT (CTO SI); Initial schematic development and format changes; Added DIP for SJA1110 boot options.; Fixed bug where Reset pin from Debug header; Removed two extra caps at SJA1110 VDDIO_GPIO2025-09; YT (CTO SI)X9; Drawing Title:; Size; Document Number; Rev; Date:; Sheet; Page Title:; Classification:; SCH-96101 PDF: SPF-96101; X-MR-NAVQ95E-T1S; Monday, September 29, 2025; <Classification>

Replaced Cortex Debug with right-angle.
Added level shifter to 1V8 for MDIO

was not connected. Improved power network
around SJA1110

Added custom pre-programmed PN for PF5103.
Fixed PGOOD LED circuit.
